blerchin/hangprinter/doc/v3/media/000.jpg

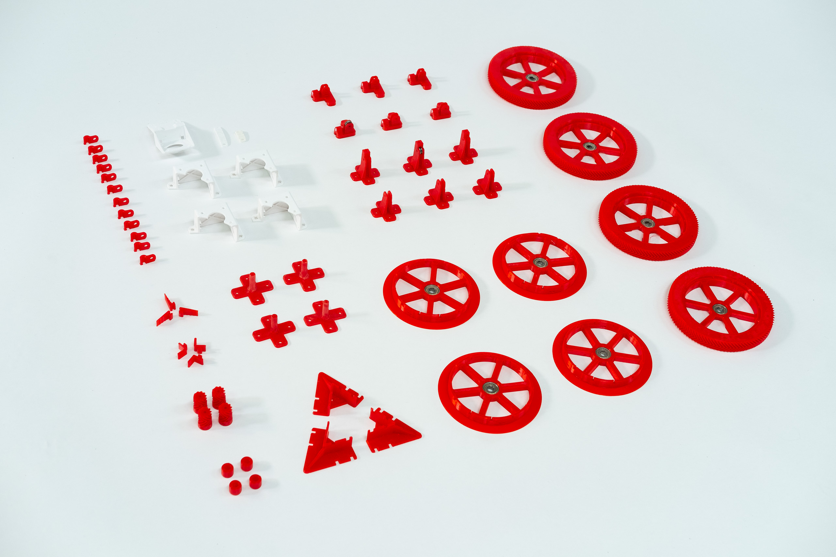
doc/v3/media/000.jpg
