blerchin/hangprinter/doc/v3/media/001.jpg

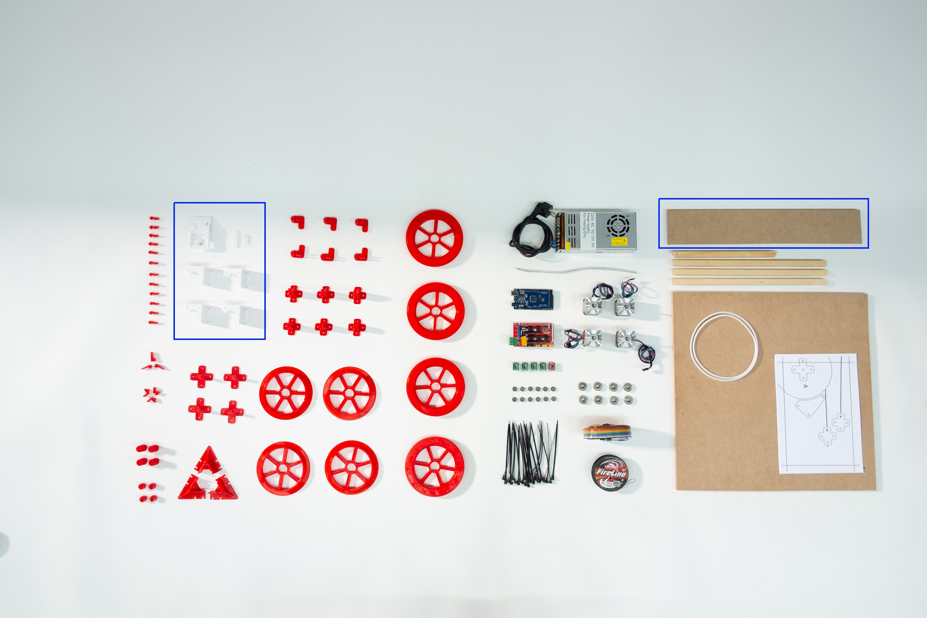
doc/v3/media/001.jpg
