blerchin/hangprinter/doc/v3/media/002.jpg

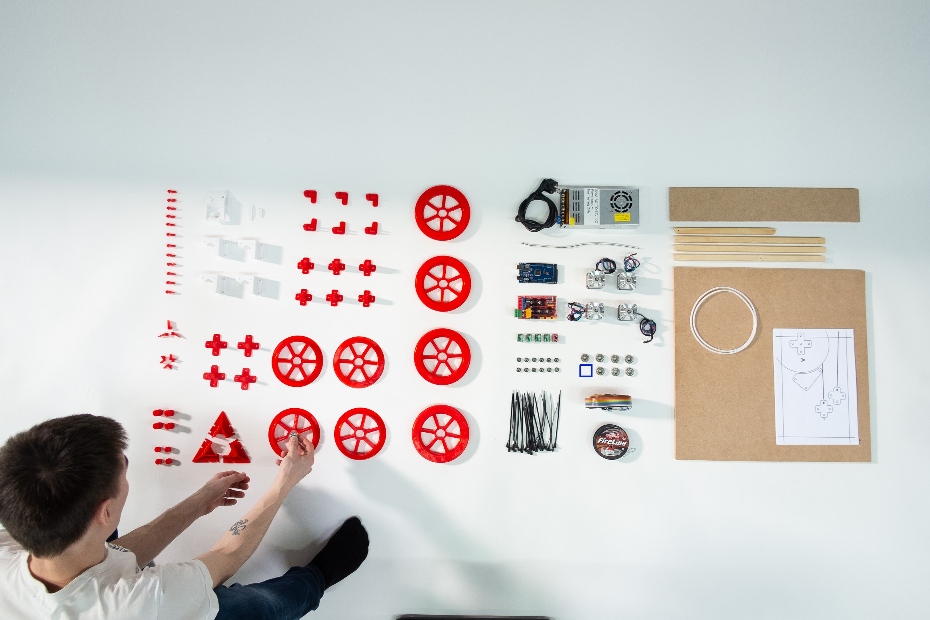
doc/v3/media/002.jpg
