blerchin/hangprinter/doc/v3/media/003.jpg

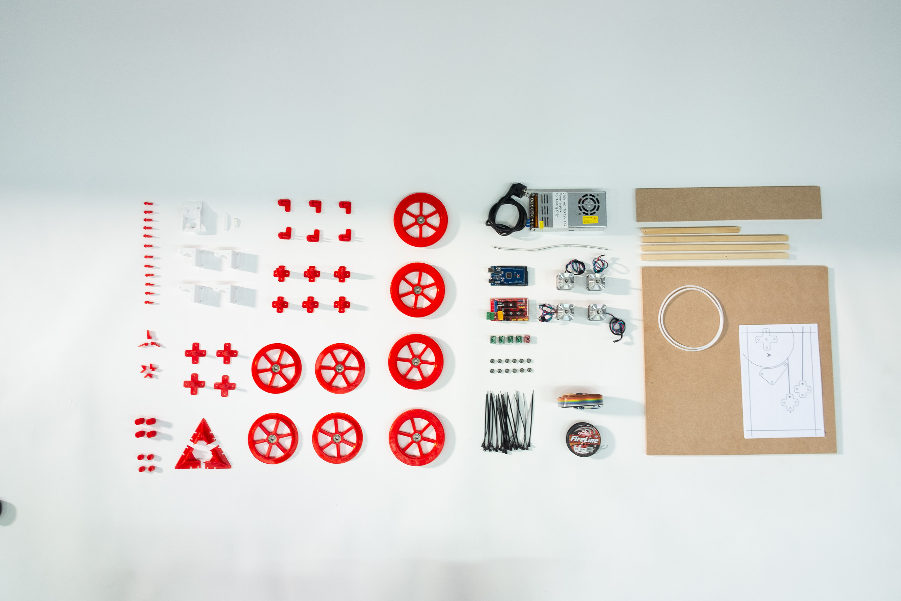
doc/v3/media/003.jpg
