blerchin/hangprinter/doc/v3/media/004.jpg

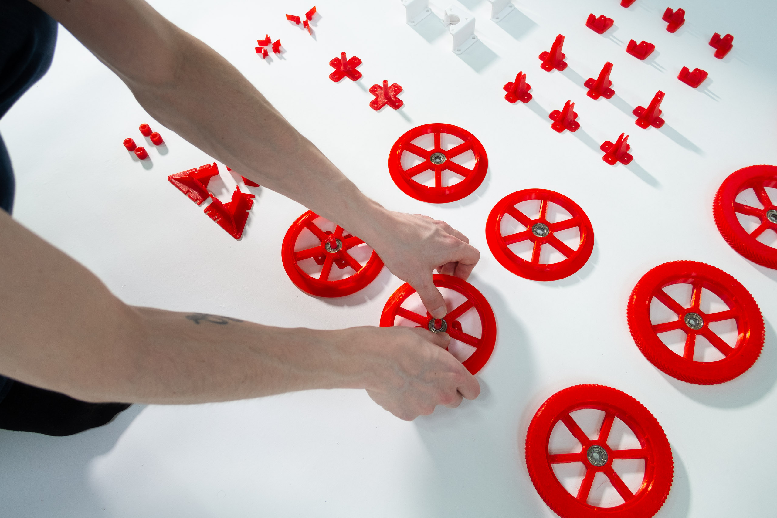
doc/v3/media/004.jpg
