blerchin/hangprinter/doc/v3/media/005.jpg

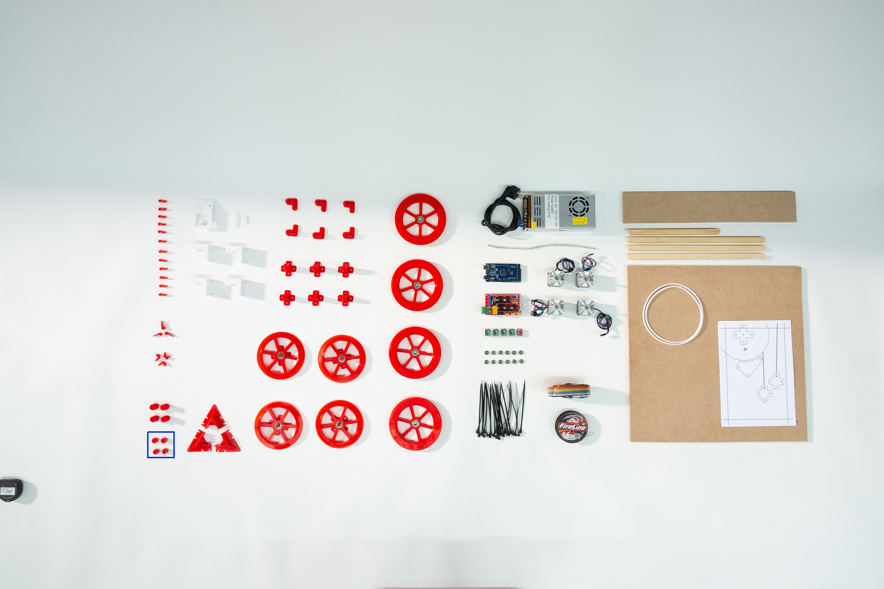
doc/v3/media/005.jpg
