blerchin/hangprinter/doc/v3/media/006.jpg

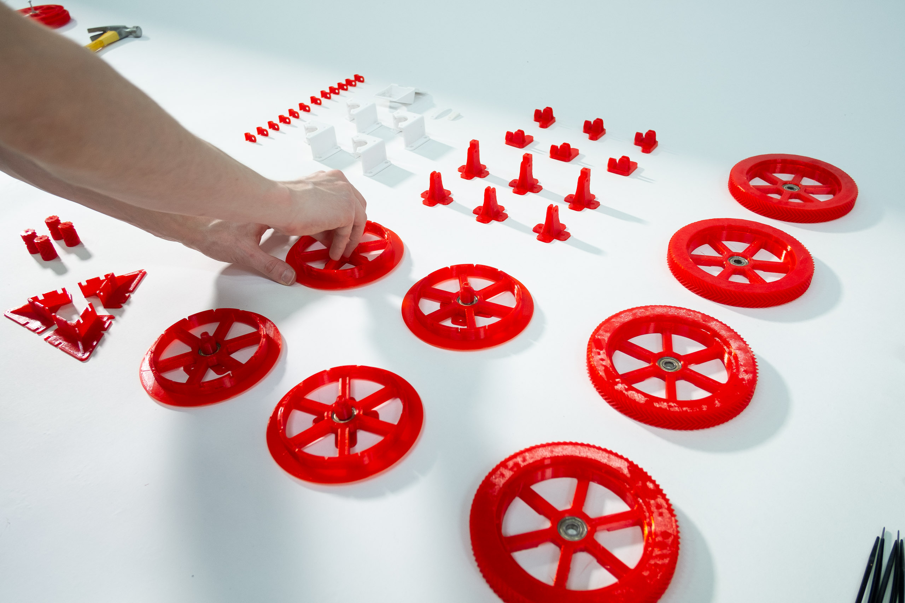
doc/v3/media/006.jpg
