blerchin/hangprinter/doc/v3/media/007.jpg

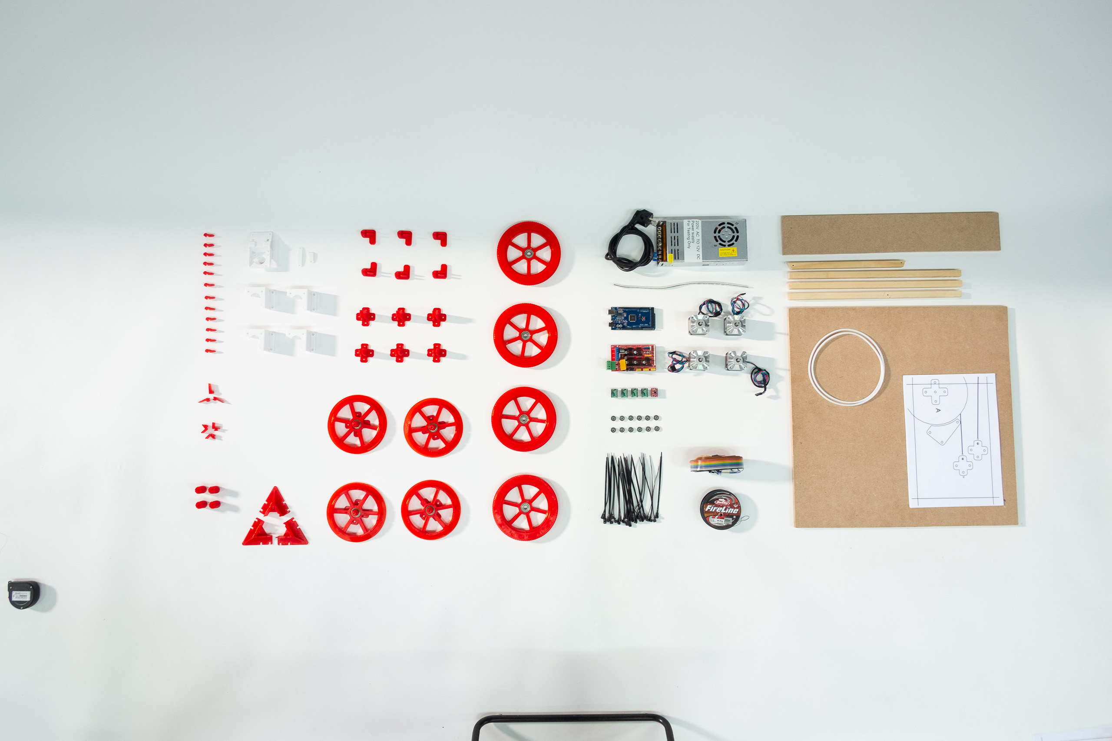
doc/v3/media/007.jpg
