blerchin/hangprinter/doc/v3/media/008.jpg

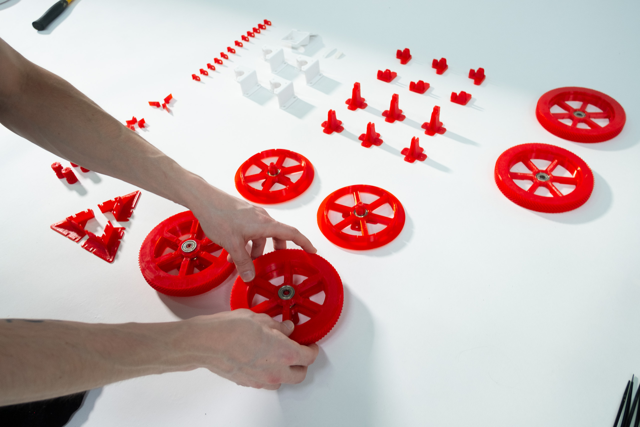
doc/v3/media/008.jpg
