blerchin/hangprinter/doc/v3/media/009.jpg

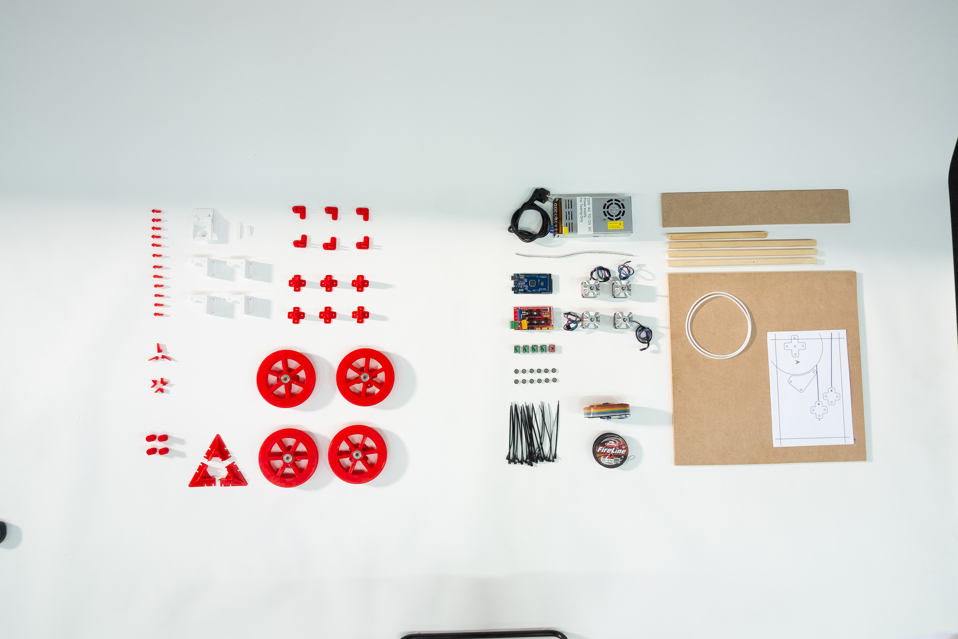
doc/v3/media/009.jpg
