blerchin/hangprinter/doc/v3/media/010.jpg

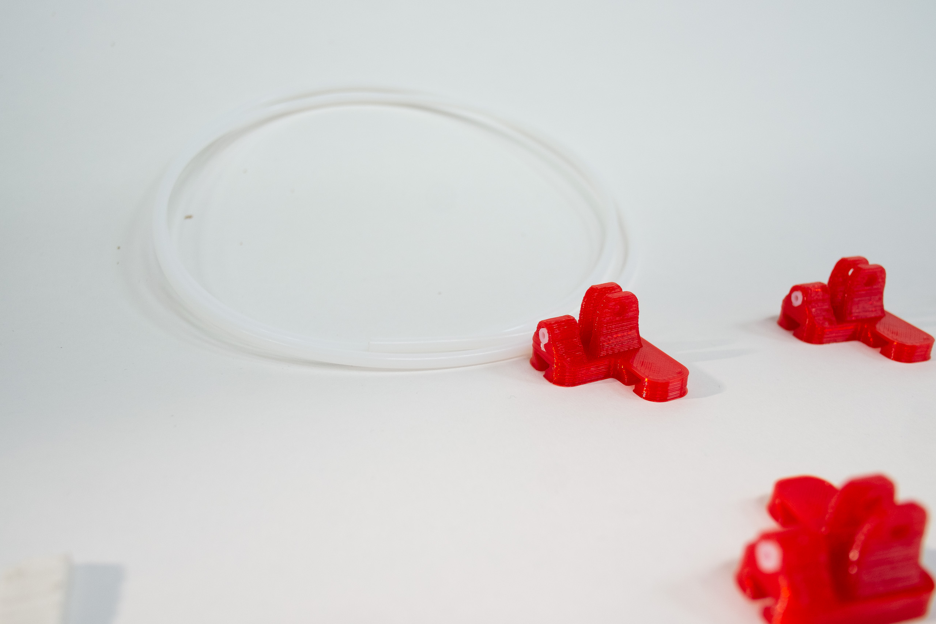
doc/v3/media/010.jpg
