blerchin/hangprinter/doc/v3/media/011.jpg

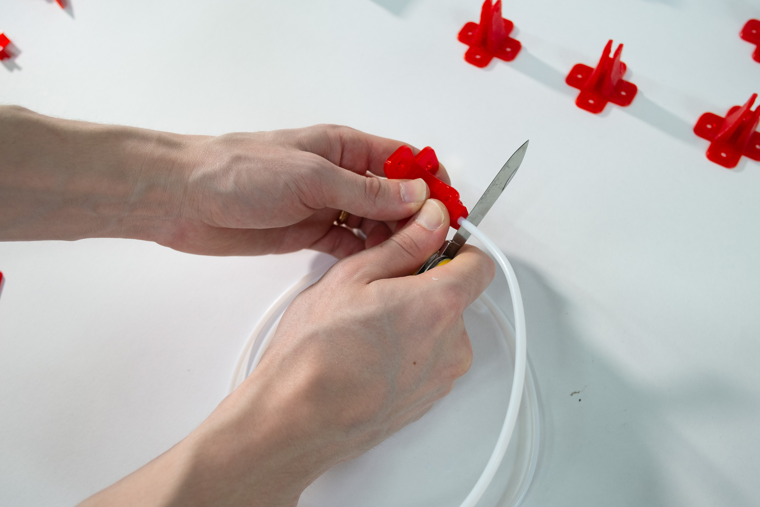
doc/v3/media/011.jpg
