blerchin/hangprinter/doc/v3/media/012.jpg

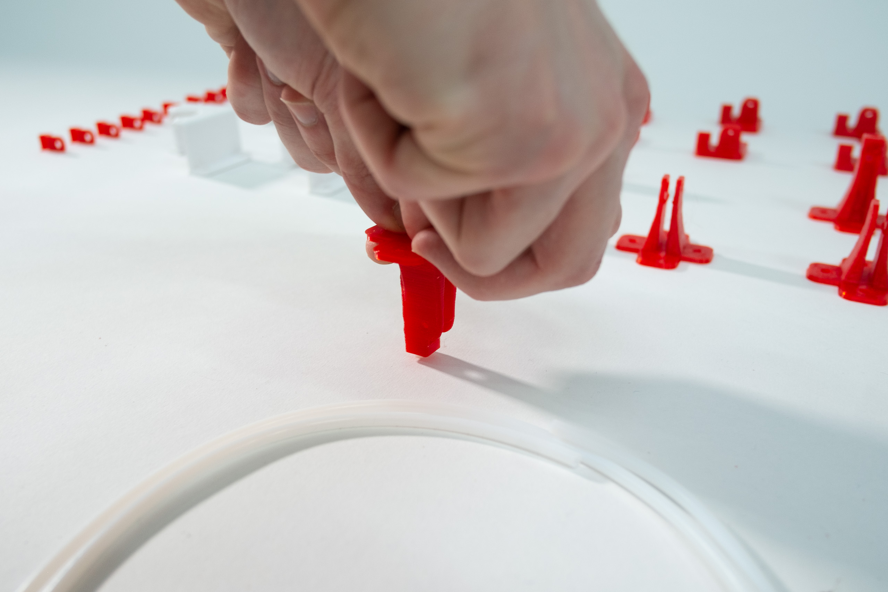
doc/v3/media/012.jpg
