blerchin/hangprinter/doc/v3/media/013.jpg

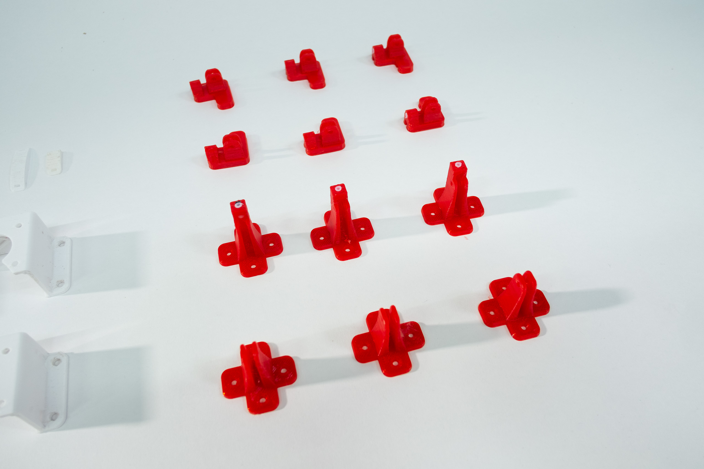
doc/v3/media/013.jpg
