blerchin/hangprinter/doc/v3/media/014.jpg

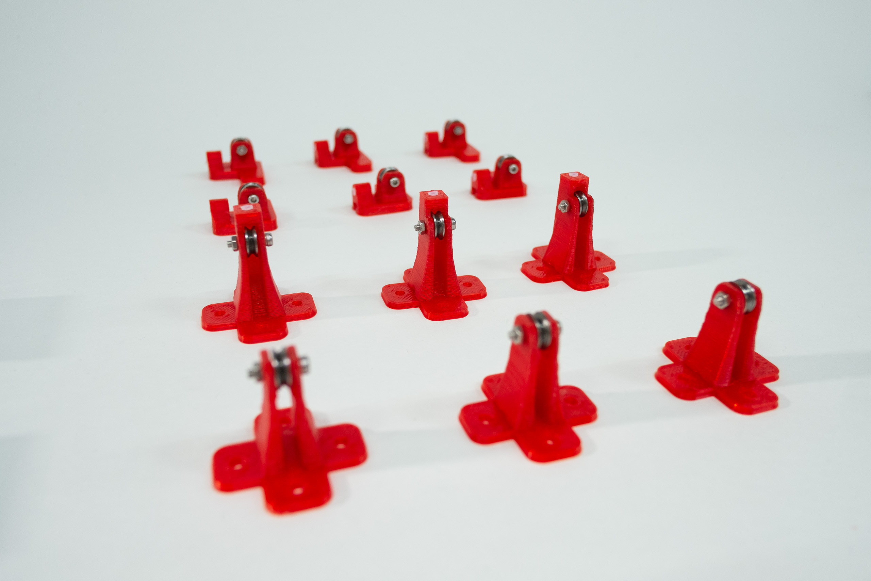
doc/v3/media/014.jpg
