blerchin/hangprinter/doc/v3/media/015.jpg

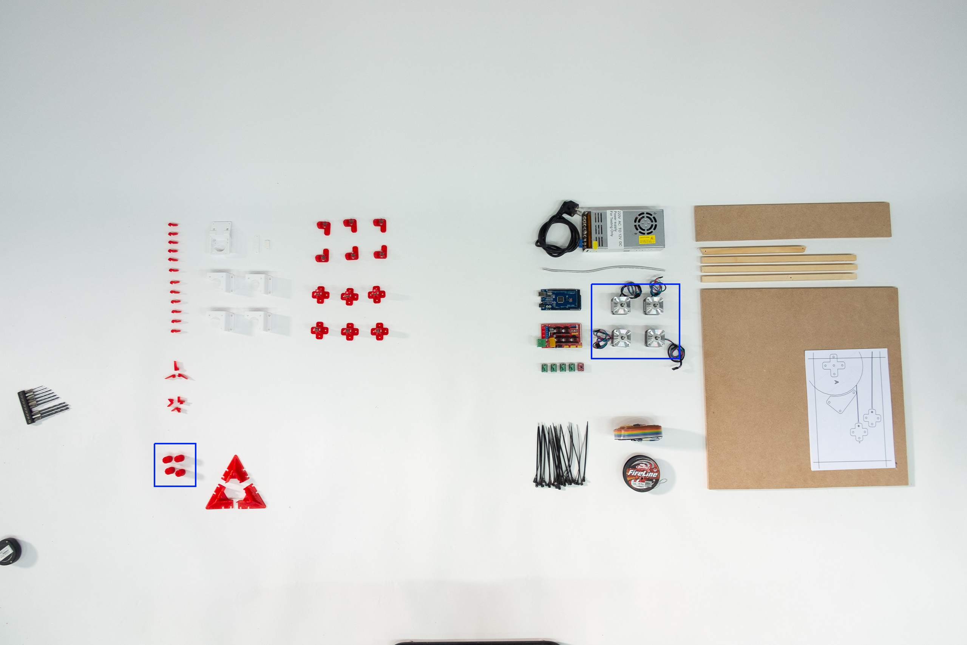
doc/v3/media/015.jpg
