blerchin/hangprinter/doc/v3/media/016.jpg

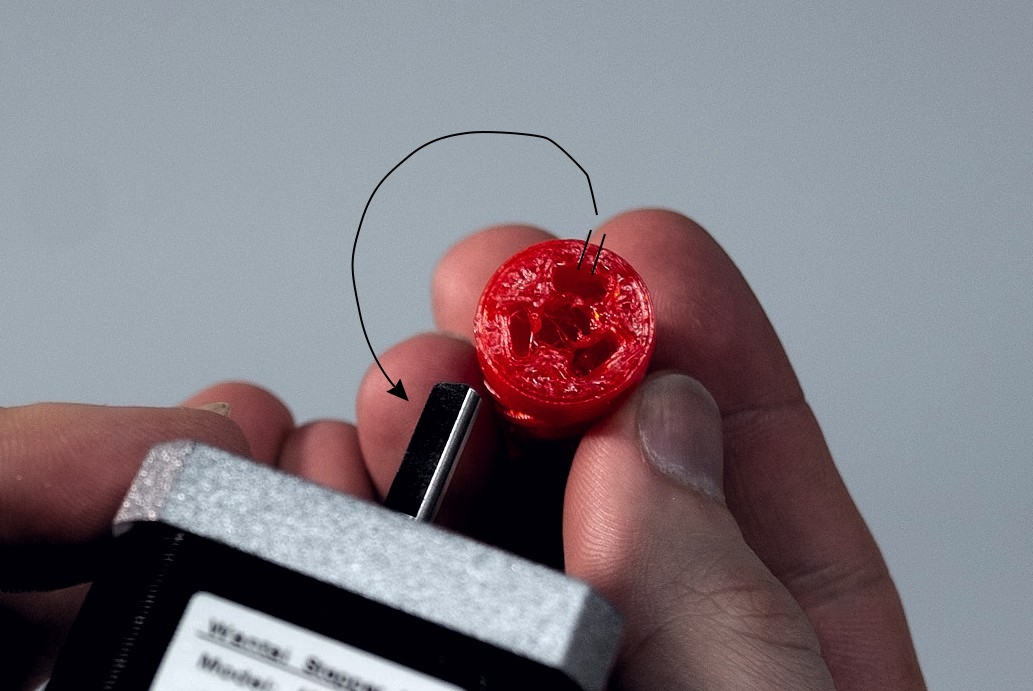
doc/v3/media/016.jpg
