blerchin/hangprinter/doc/v3/media/017.jpg

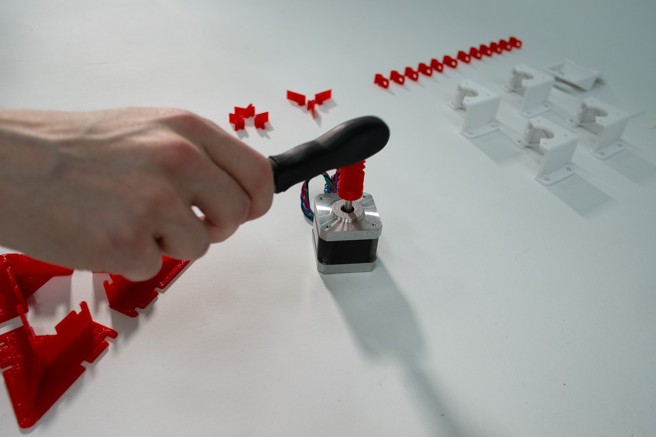
doc/v3/media/017.jpg
