blerchin/hangprinter/doc/v3/media/018.jpg

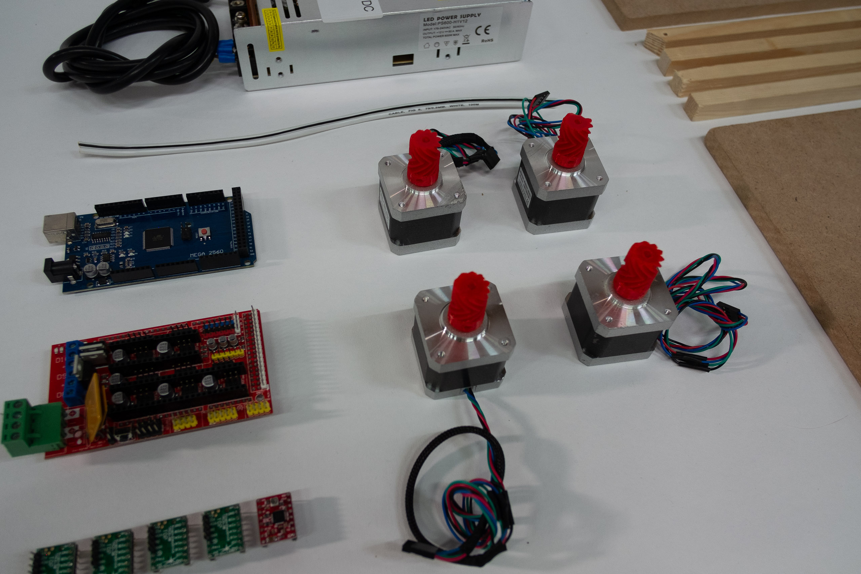
doc/v3/media/018.jpg
