blerchin/hangprinter/doc/v3/media/019.jpg

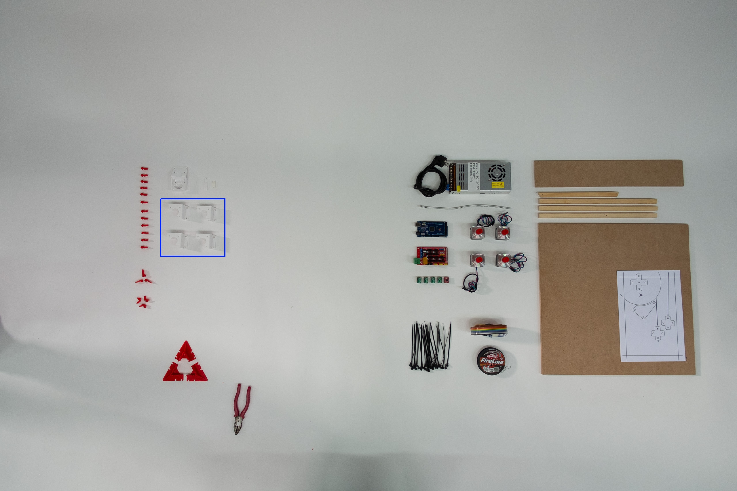
doc/v3/media/019.jpg
