blerchin/hangprinter/doc/v3/media/020.jpg

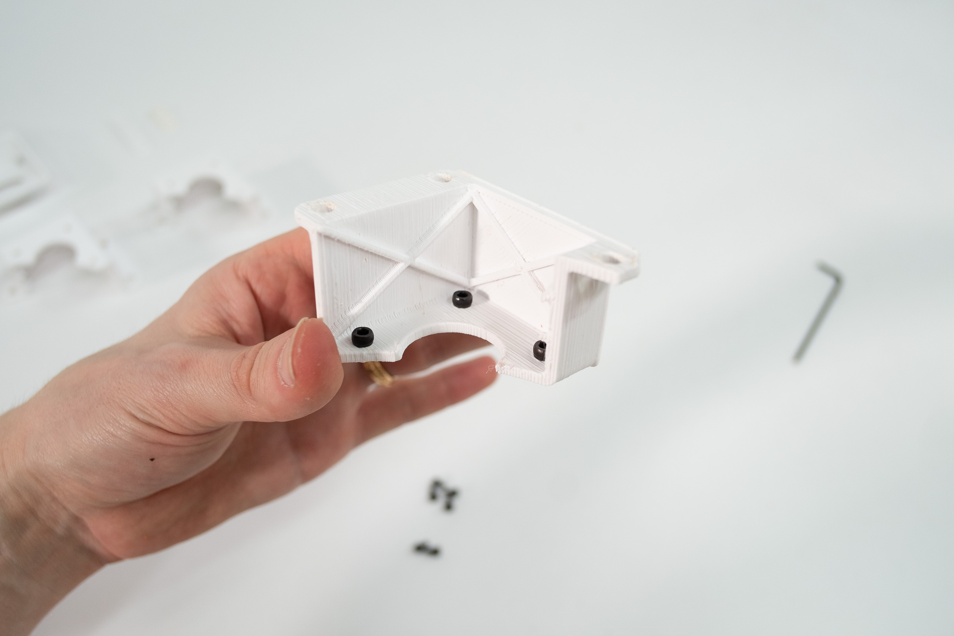
doc/v3/media/020.jpg
