blerchin/hangprinter/doc/v3/media/021.jpg

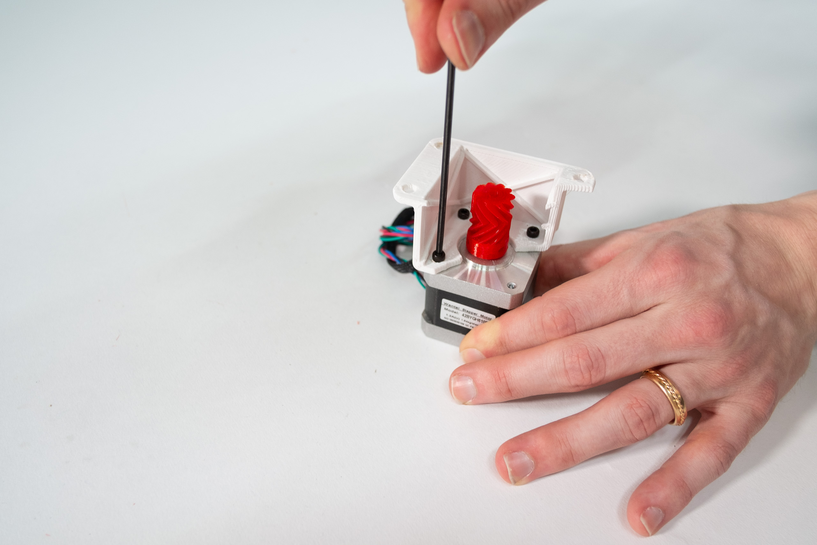
doc/v3/media/021.jpg
