blerchin/hangprinter/doc/v3/media/022.jpg

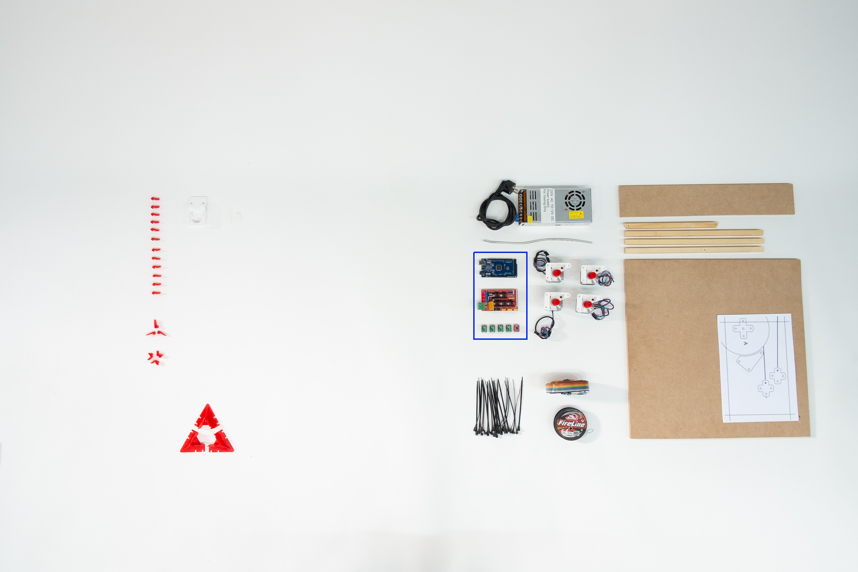
doc/v3/media/022.jpg
