blerchin/hangprinter/doc/v3/media/023.jpg

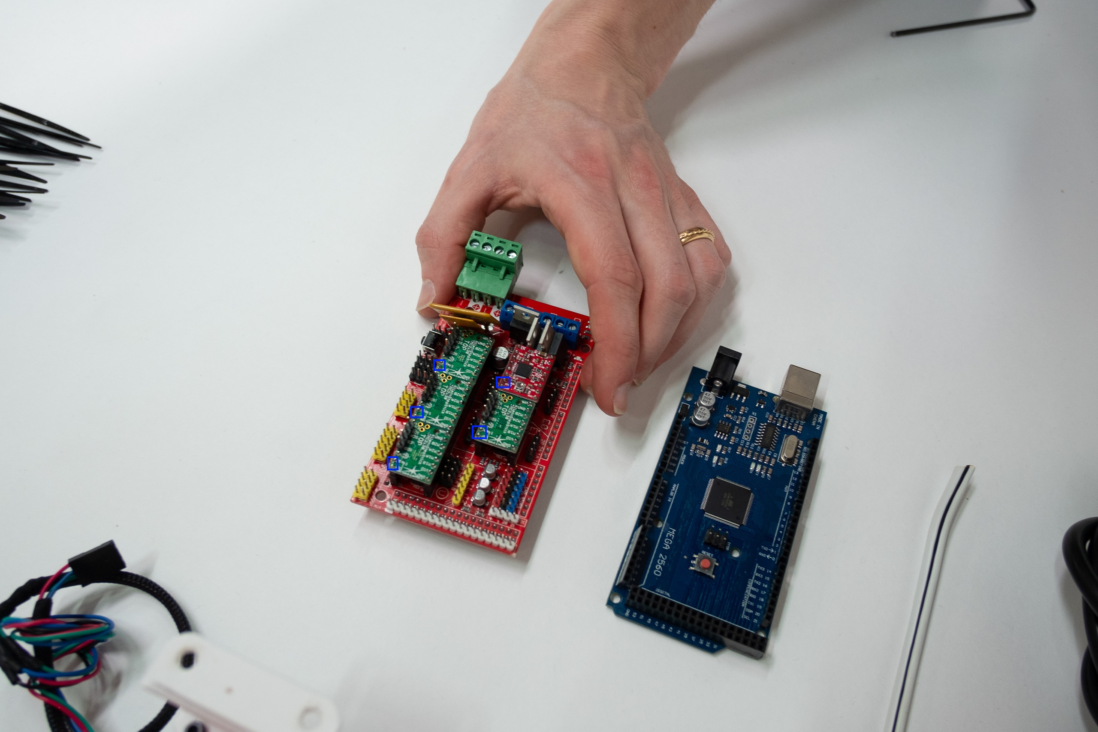
doc/v3/media/023.jpg
