blerchin/hangprinter/doc/v3/media/024.jpg

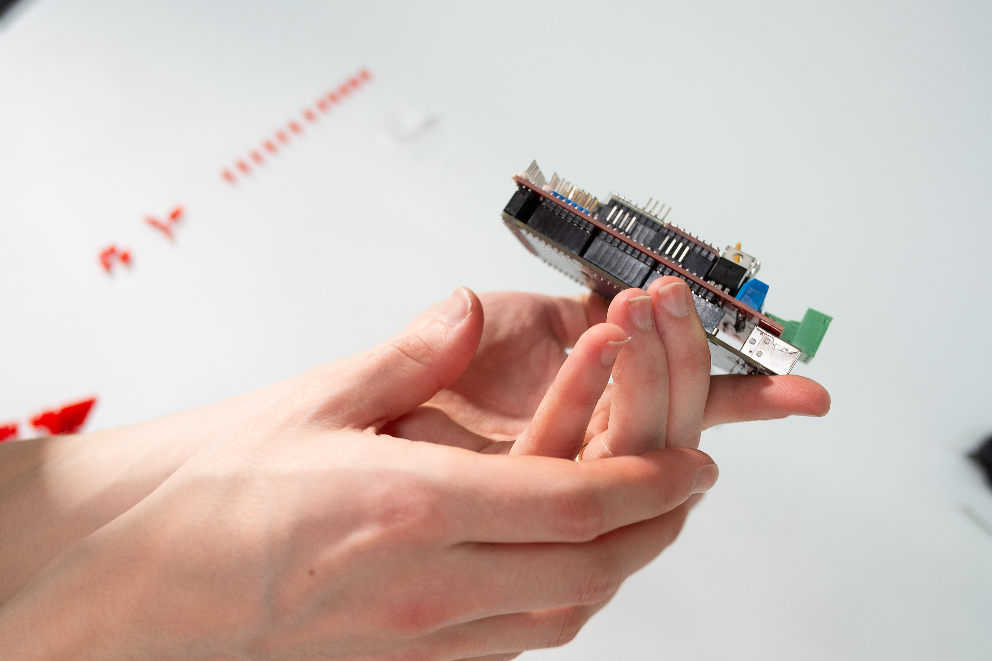
doc/v3/media/024.jpg
