blerchin/hangprinter/doc/v3/media/025.jpg

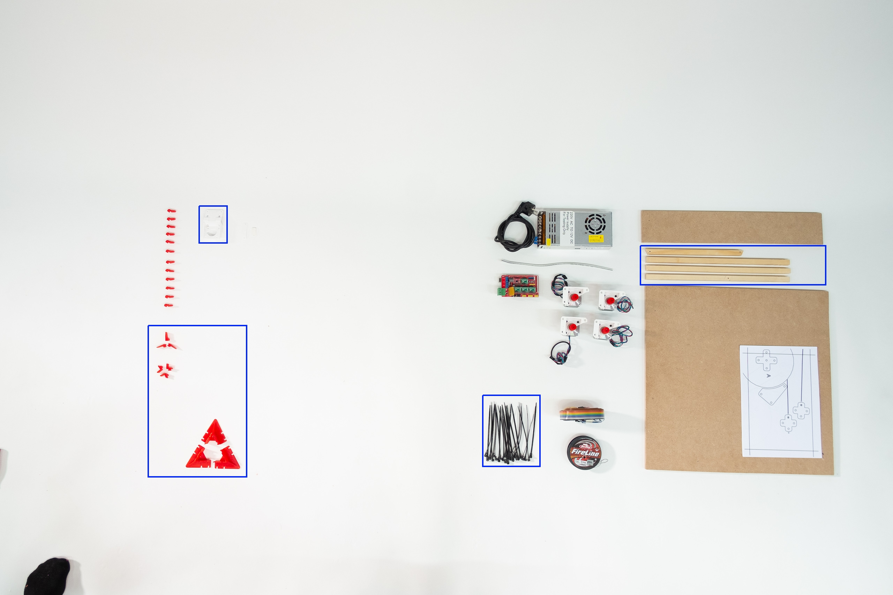
doc/v3/media/025.jpg
