blerchin/hangprinter/doc/v3/media/026.jpg

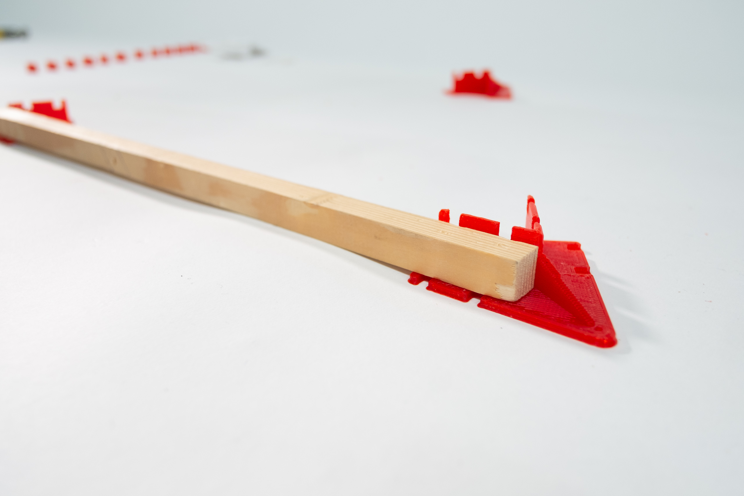
doc/v3/media/026.jpg
