blerchin/hangprinter/doc/v3/media/027.jpg

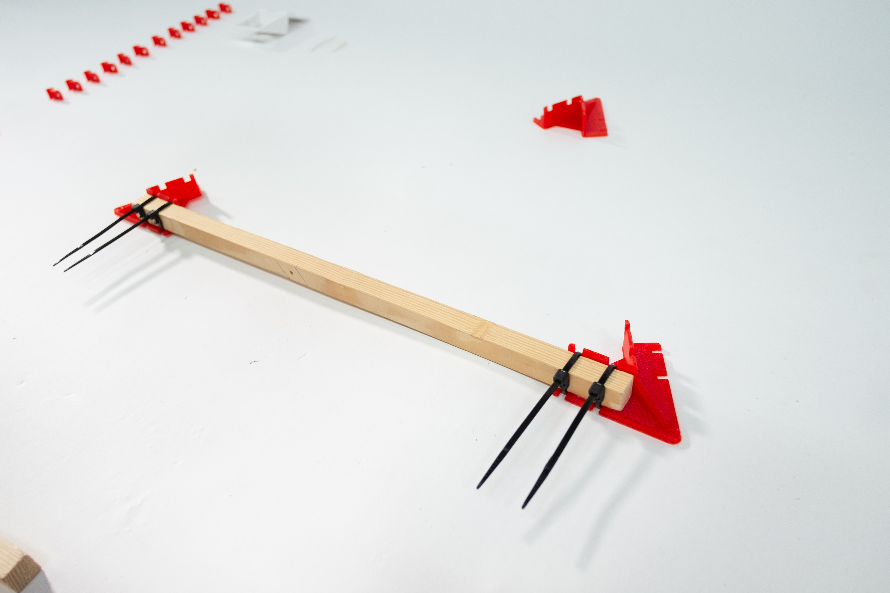
doc/v3/media/027.jpg
