blerchin/hangprinter/doc/v3/media/028.jpg

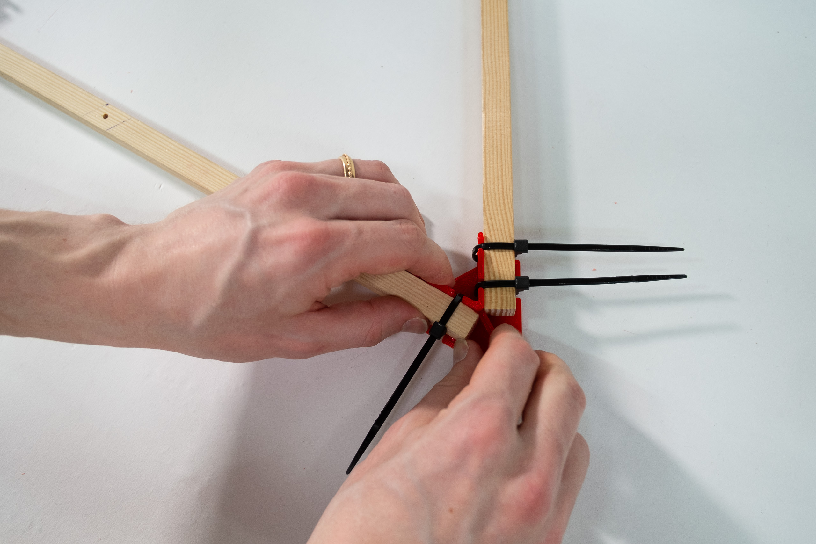
doc/v3/media/028.jpg
