blerchin/hangprinter/doc/v3/media/029.jpg

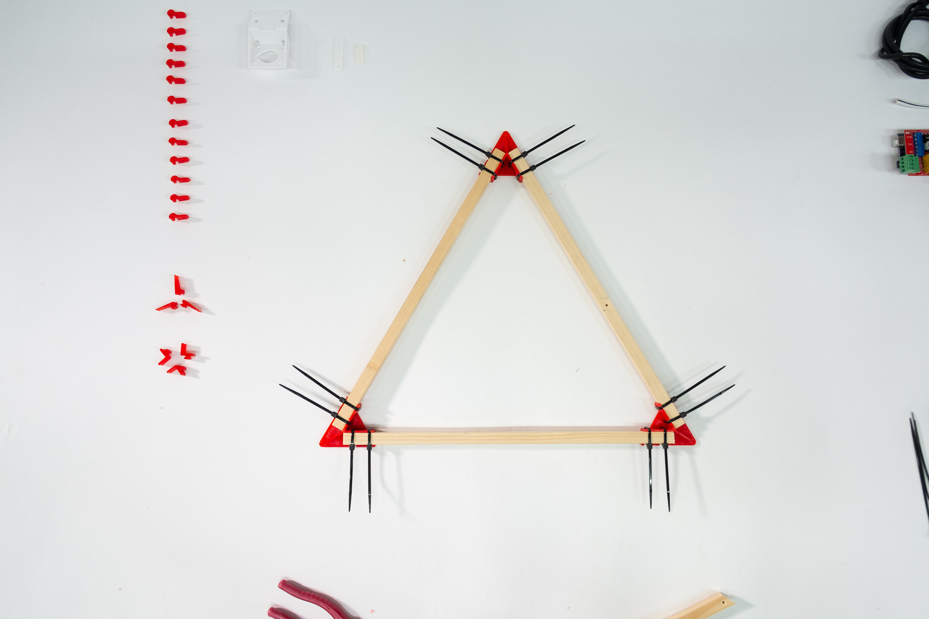
doc/v3/media/029.jpg
