blerchin/hangprinter/doc/v3/media/030.jpg

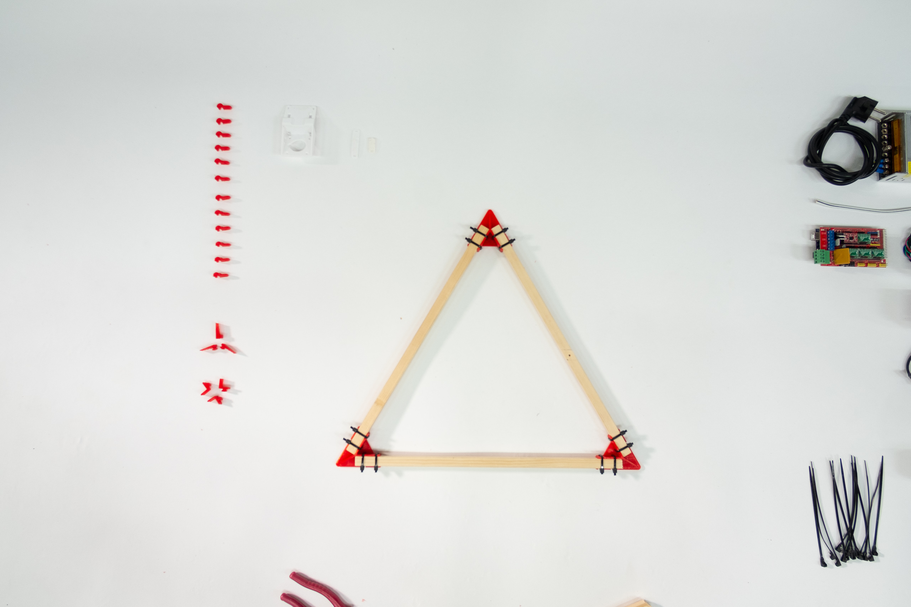
doc/v3/media/030.jpg
