blerchin/hangprinter/doc/v3/media/031.jpg

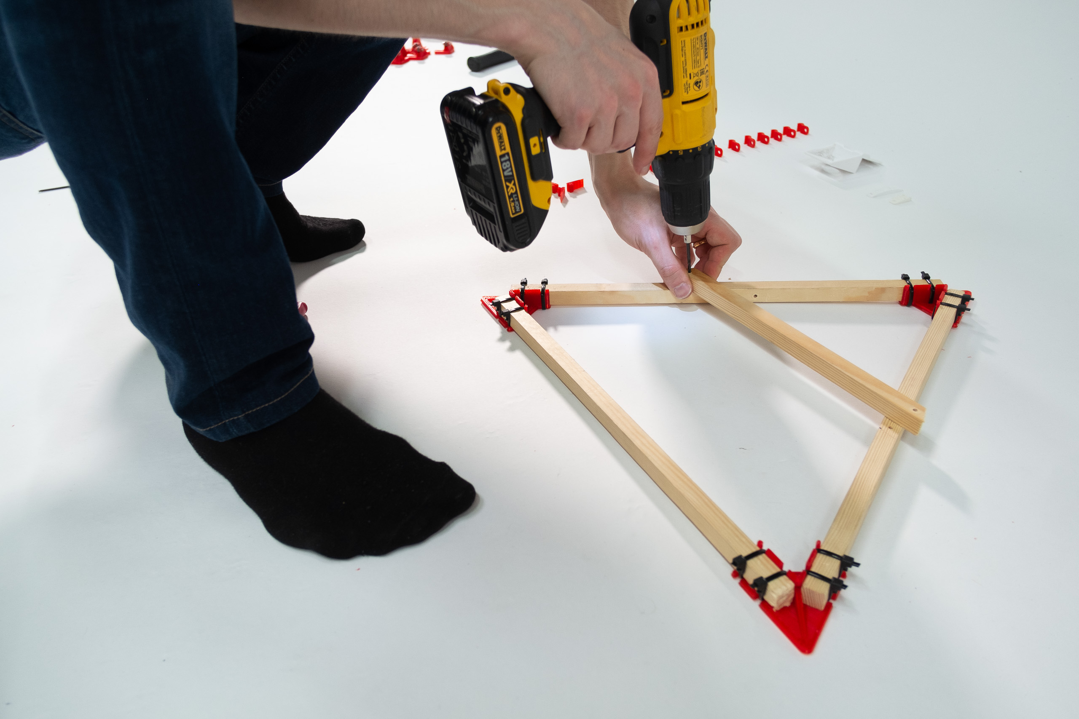
doc/v3/media/031.jpg
