blerchin/hangprinter/doc/v3/media/032.jpg

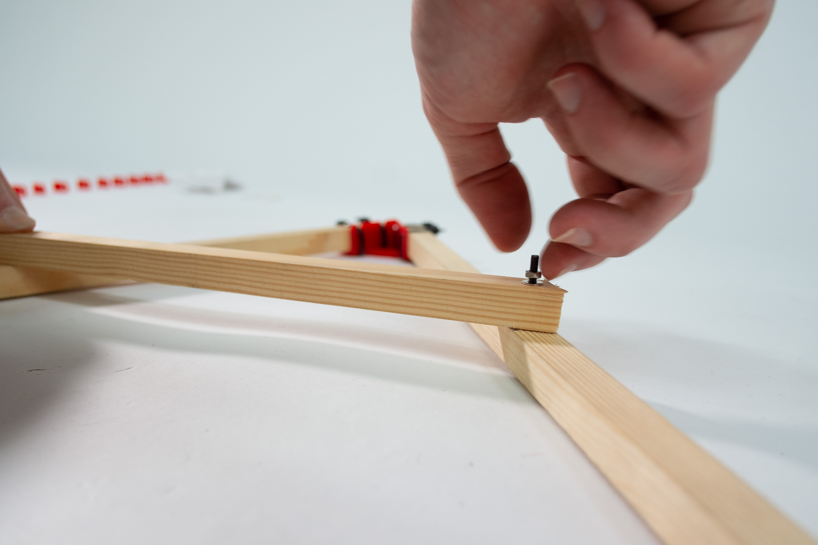
doc/v3/media/032.jpg
