blerchin/hangprinter/doc/v3/media/033.jpg

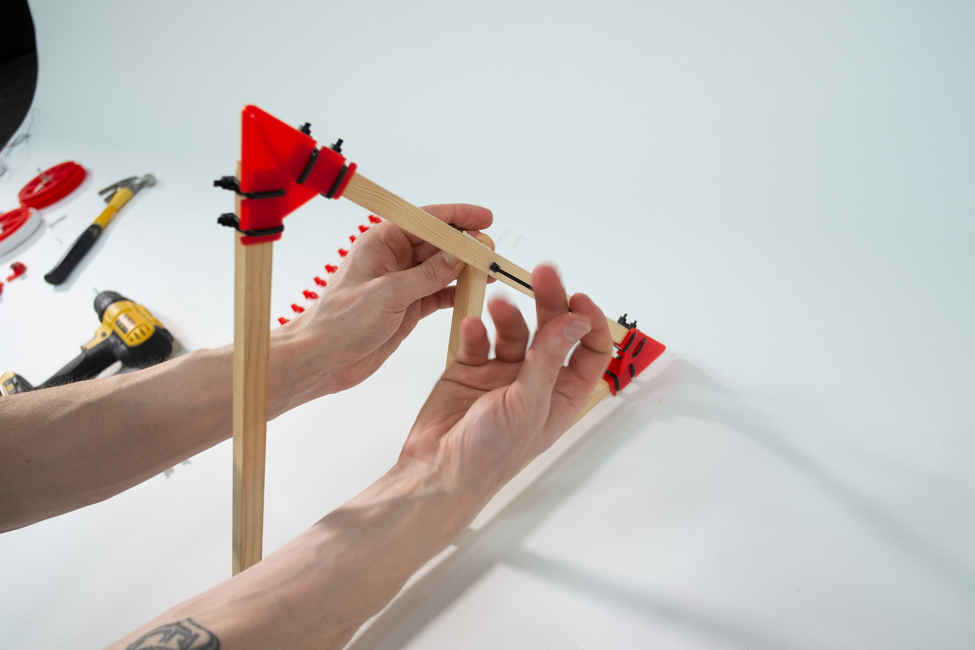
doc/v3/media/033.jpg
