blerchin/hangprinter/doc/v3/media/034.jpg

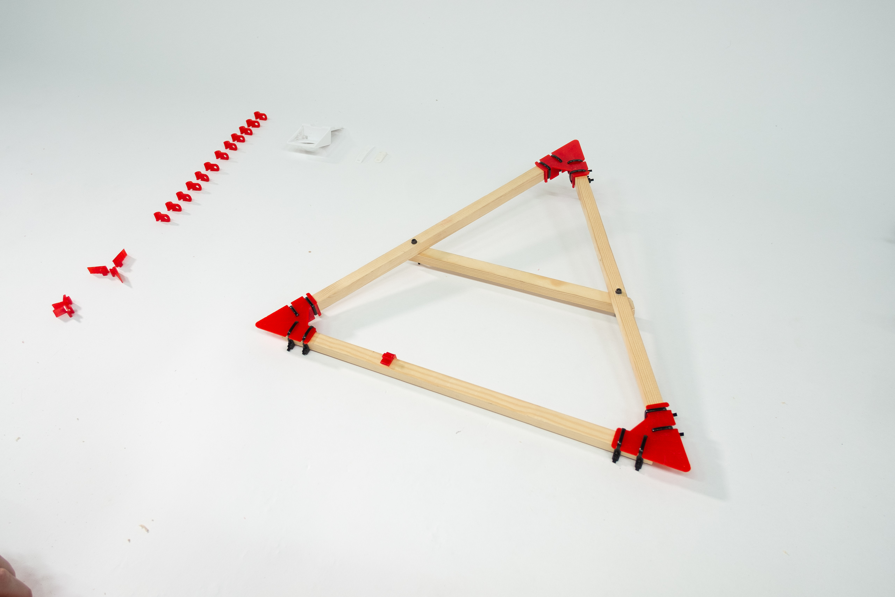
doc/v3/media/034.jpg
