blerchin/hangprinter/doc/v3/media/035.jpg

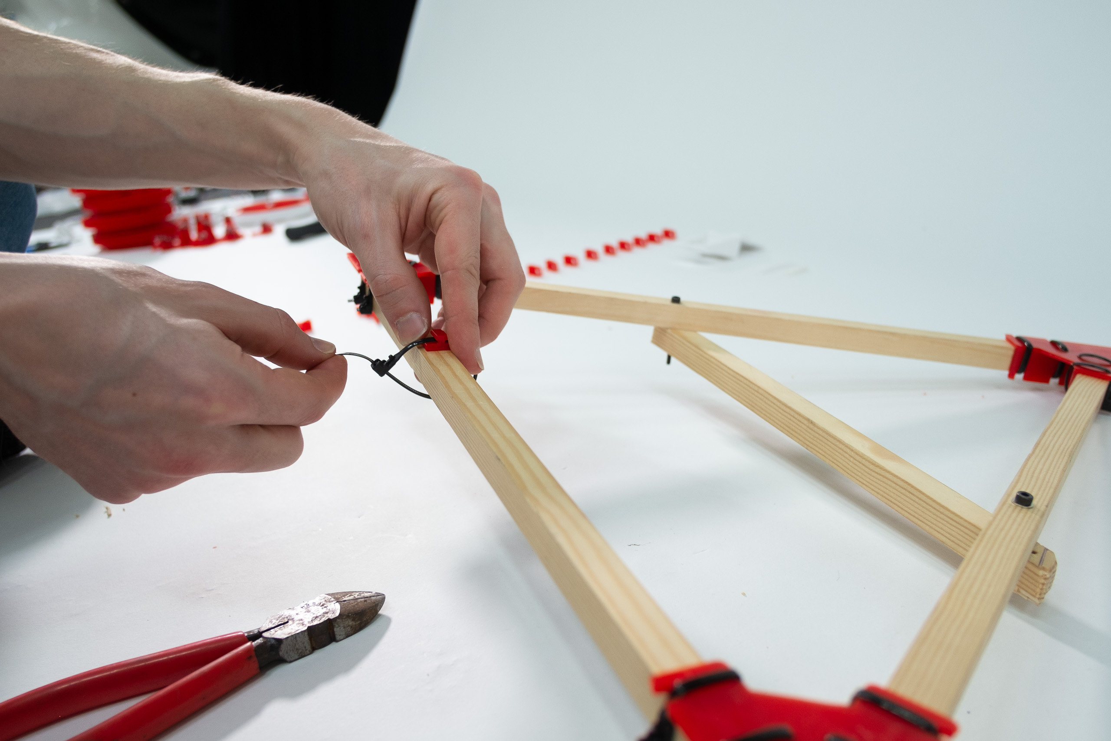
doc/v3/media/035.jpg
