blerchin/hangprinter/doc/v3/media/036.jpg

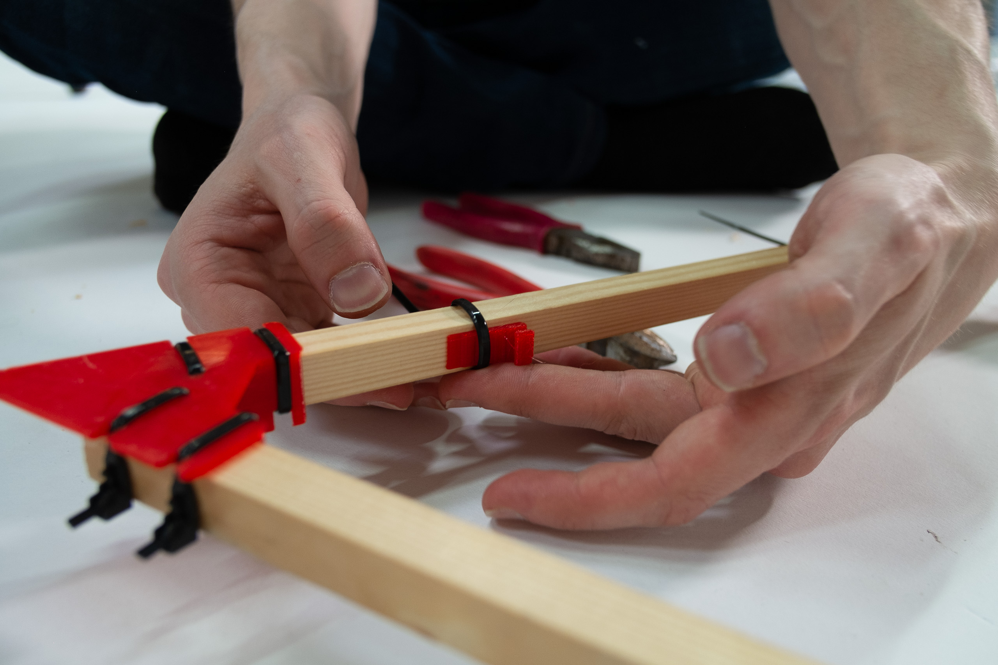
doc/v3/media/036.jpg
