blerchin/hangprinter/doc/v3/media/037.jpg

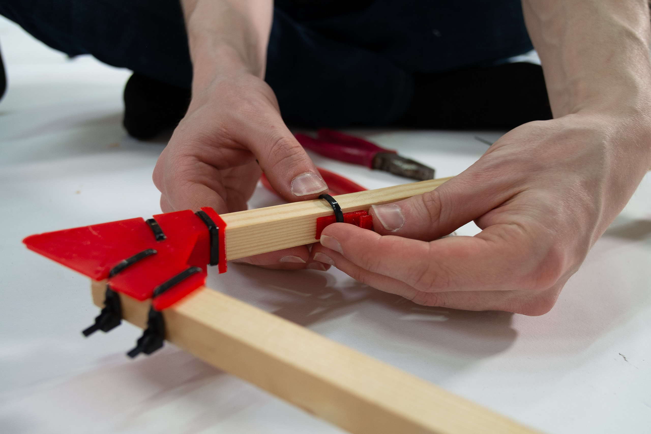
doc/v3/media/037.jpg
