blerchin/hangprinter/doc/v3/media/038.jpg

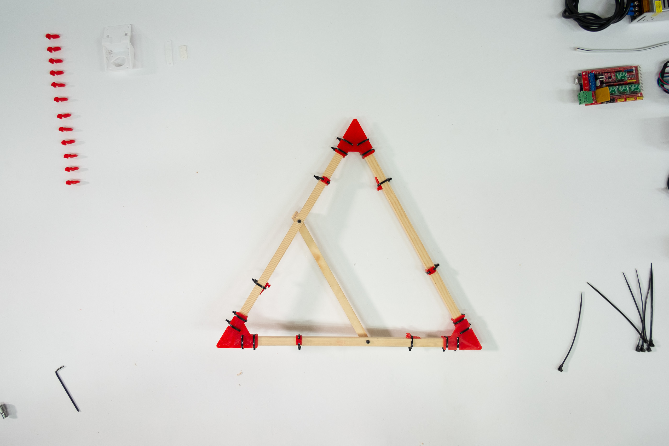
doc/v3/media/038.jpg
