blerchin/hangprinter/doc/v3/media/039.jpg

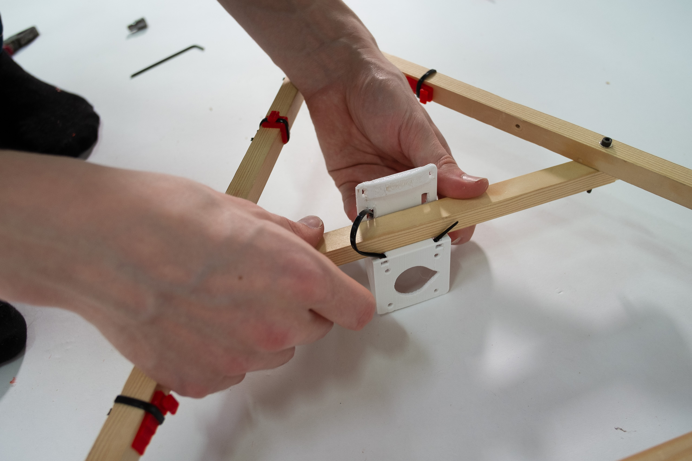
doc/v3/media/039.jpg
