blerchin/hangprinter/doc/v3/media/040.jpg

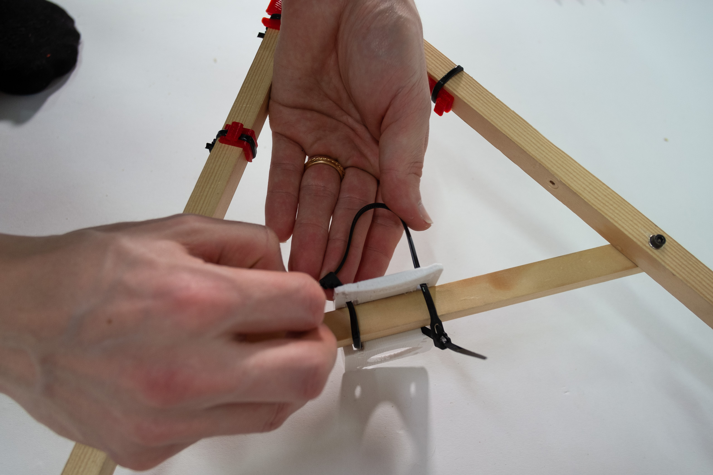
doc/v3/media/040.jpg
