blerchin/hangprinter/doc/v3/media/041.jpg

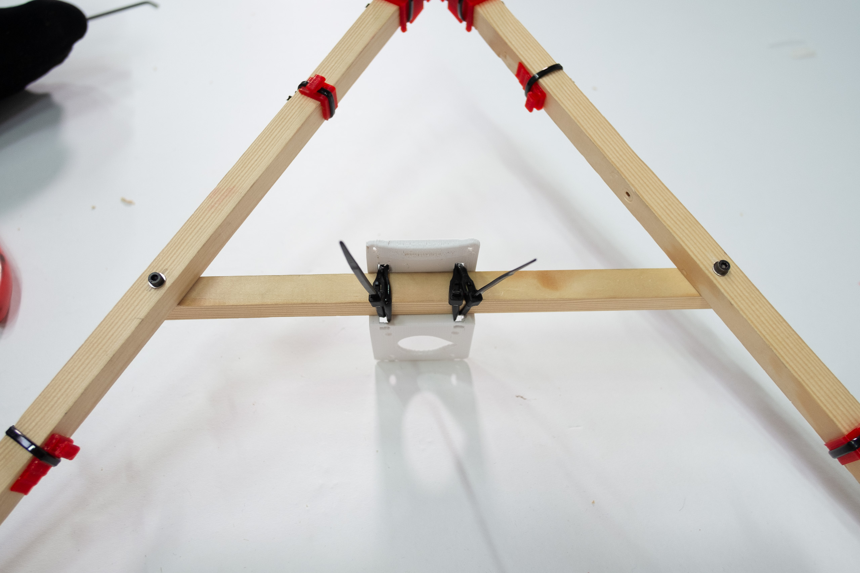
doc/v3/media/041.jpg
