blerchin/hangprinter/doc/v3/media/042.jpg

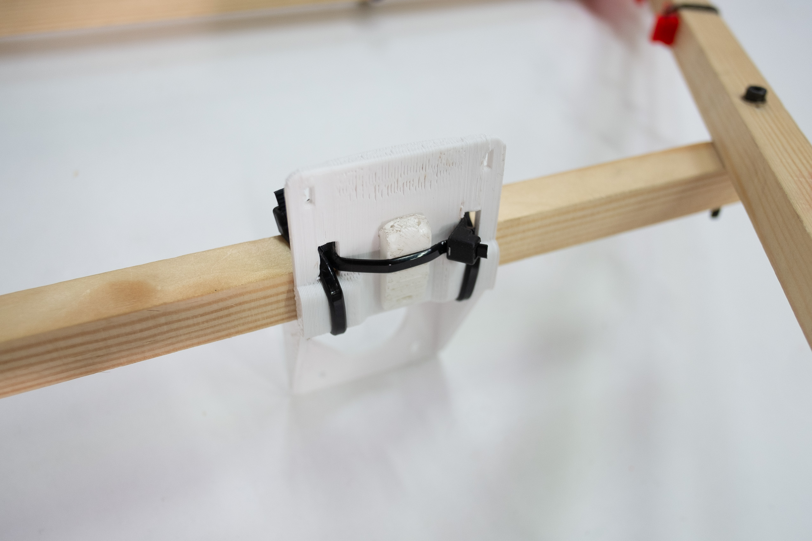
doc/v3/media/042.jpg
