blerchin/hangprinter/doc/v3/media/043.jpg

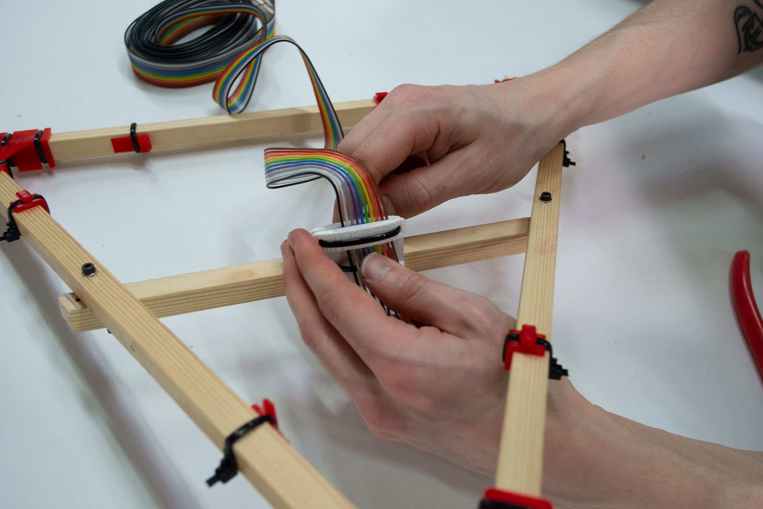
doc/v3/media/043.jpg
