blerchin/hangprinter/doc/v3/media/044.jpg

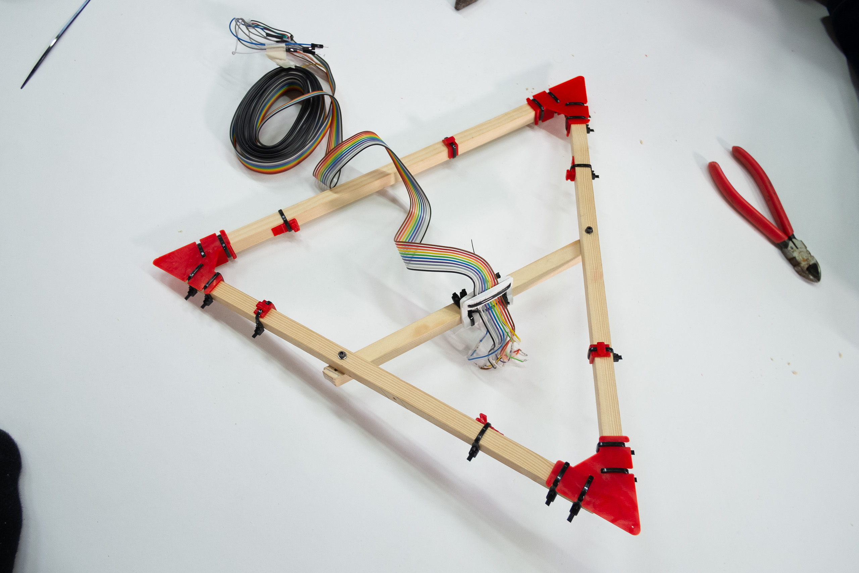
doc/v3/media/044.jpg
