blerchin/hangprinter/doc/v3/media/045.jpg

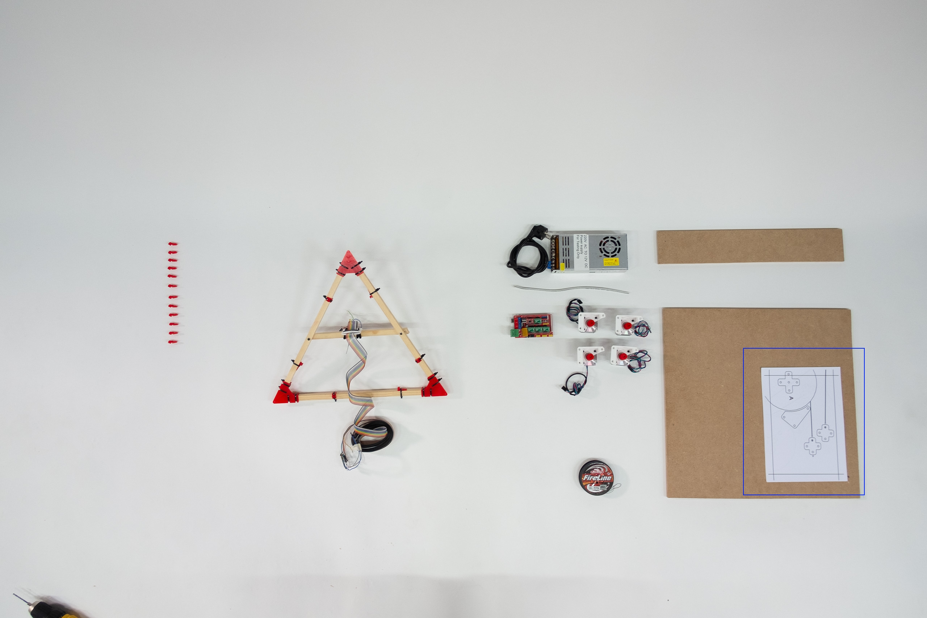
doc/v3/media/045.jpg
