blerchin/hangprinter/doc/v3/media/046.jpg

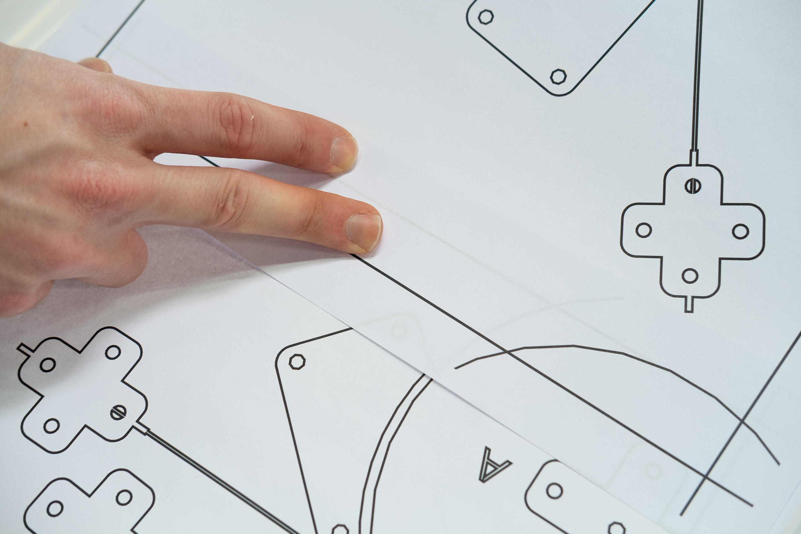
doc/v3/media/046.jpg
