blerchin/hangprinter/doc/v3/media/047.jpg

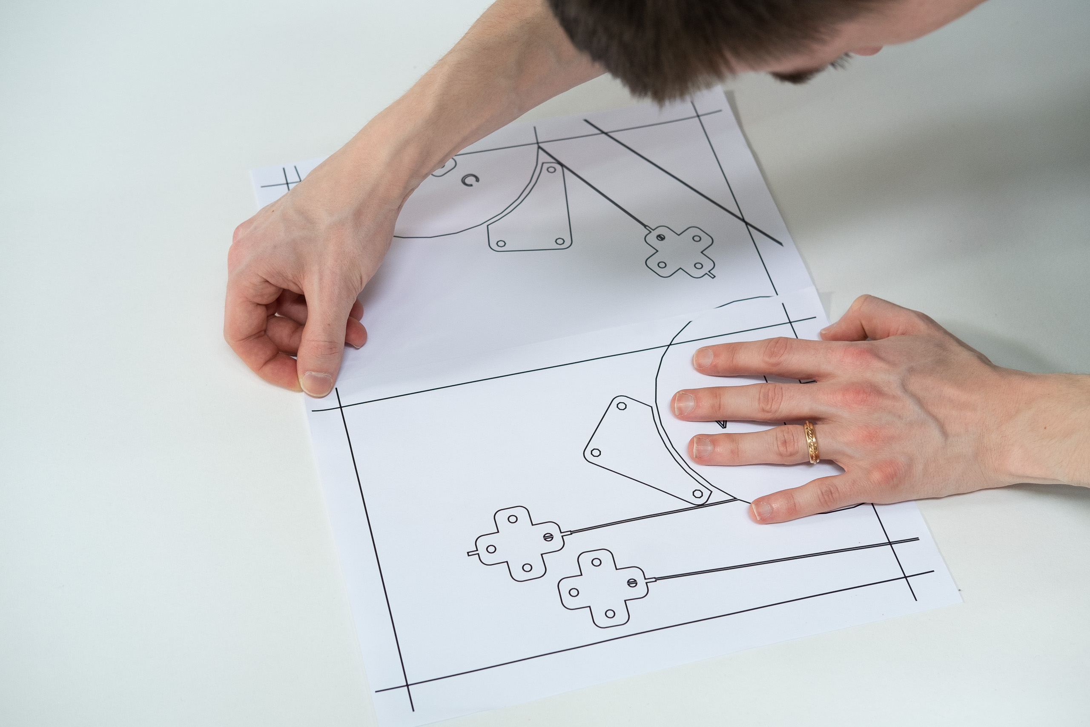
doc/v3/media/047.jpg
