blerchin/hangprinter/doc/v3/media/048.jpg

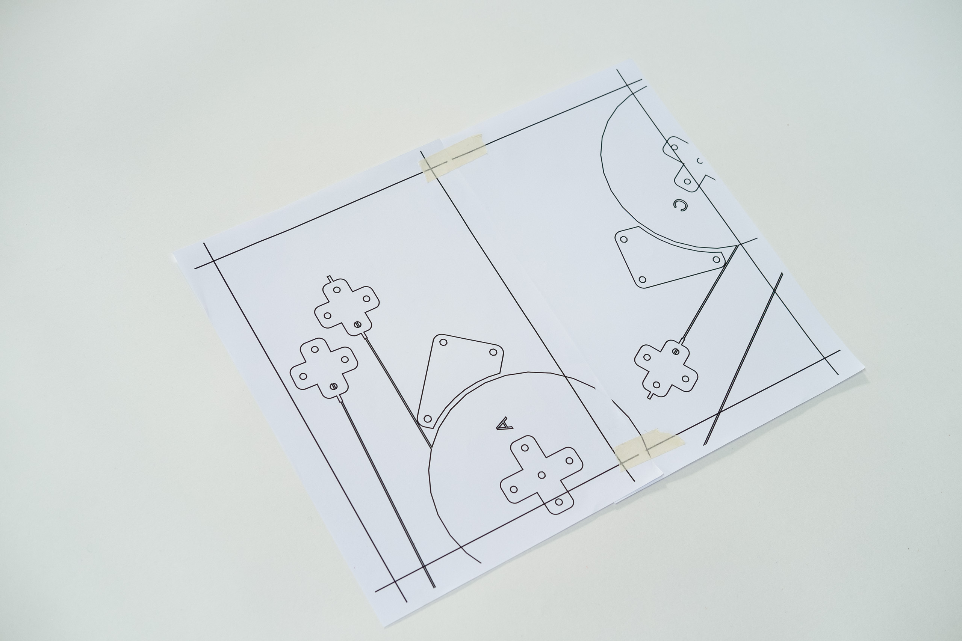
doc/v3/media/048.jpg
