blerchin/hangprinter/doc/v3/media/049.jpg

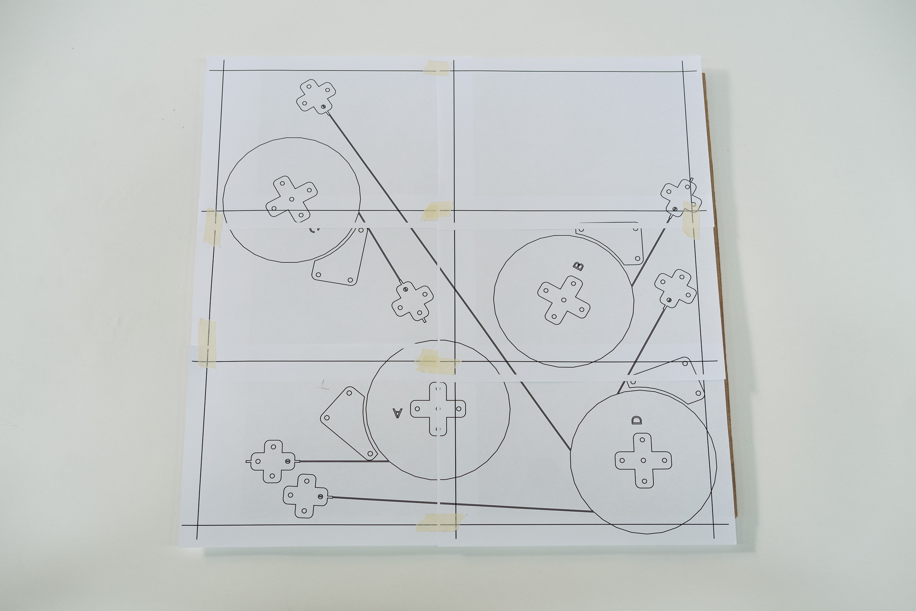
doc/v3/media/049.jpg
