blerchin/hangprinter/doc/v3/media/050.jpg

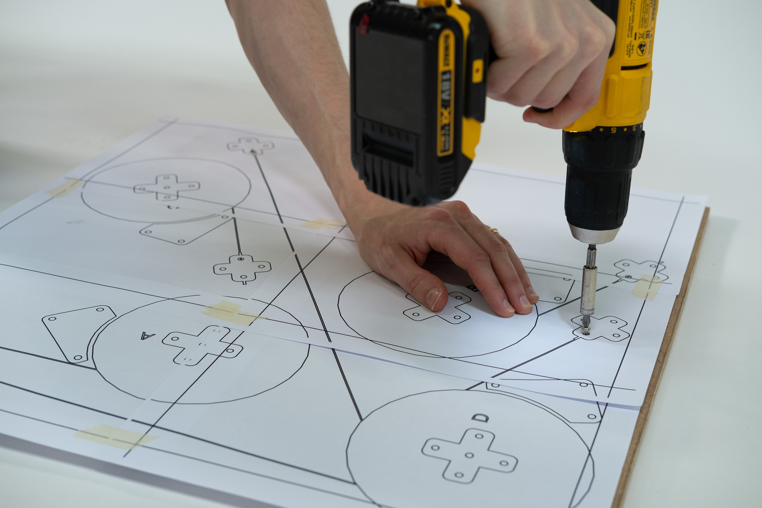
doc/v3/media/050.jpg
