blerchin/hangprinter/doc/v3/media/051.jpg

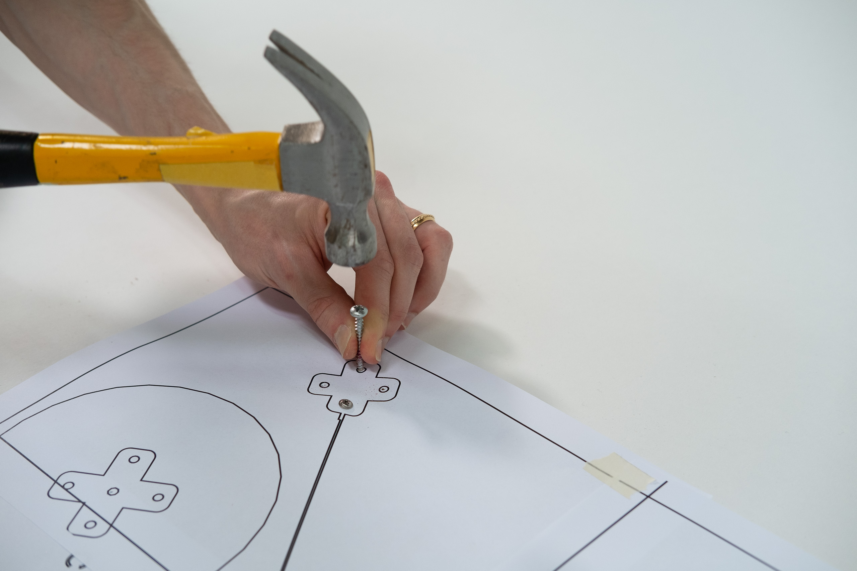
doc/v3/media/051.jpg
