blerchin/hangprinter/doc/v3/media/052.jpg

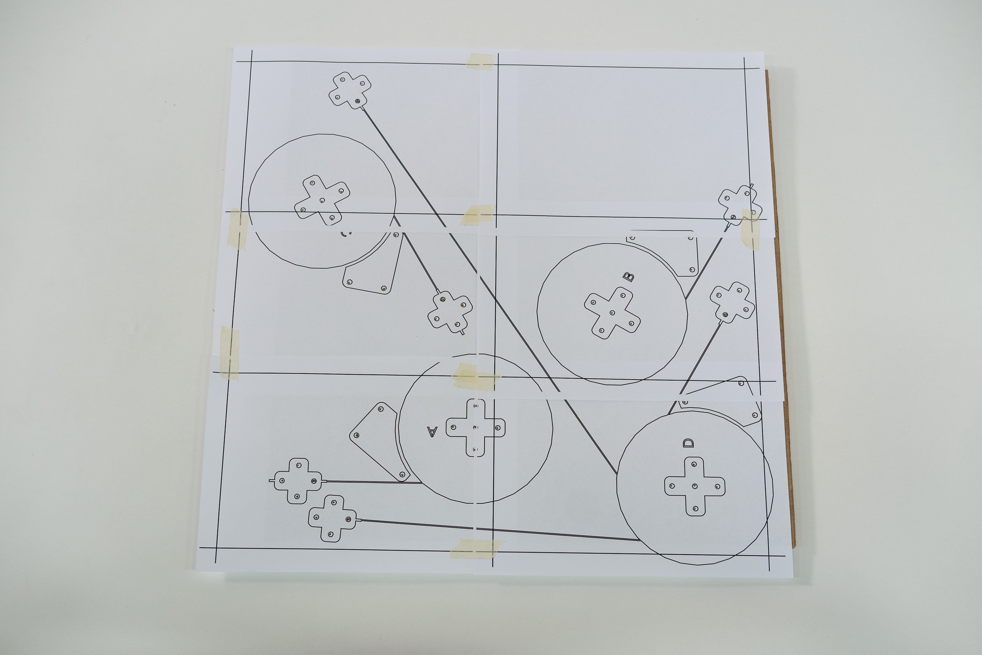
doc/v3/media/052.jpg
