blerchin/hangprinter/doc/v3/media/053.jpg

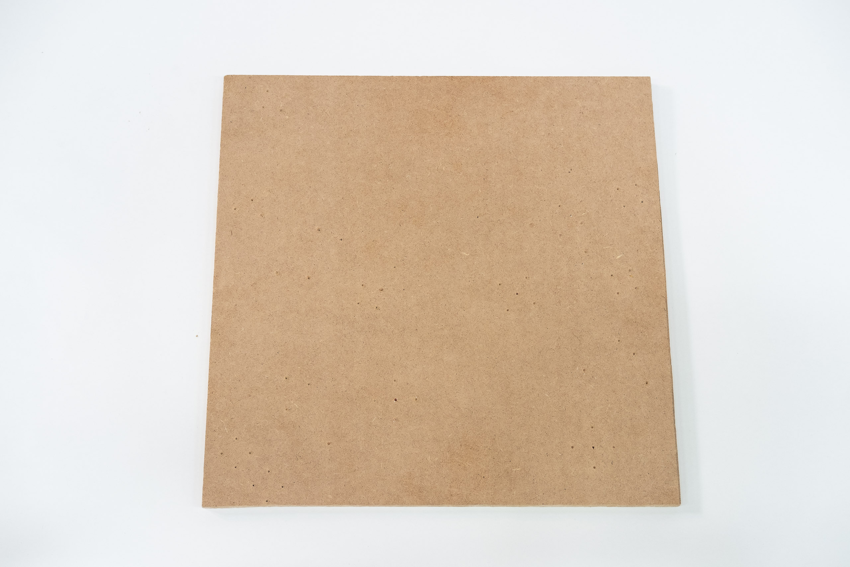
doc/v3/media/053.jpg
