blerchin/hangprinter/doc/v3/media/054.jpg

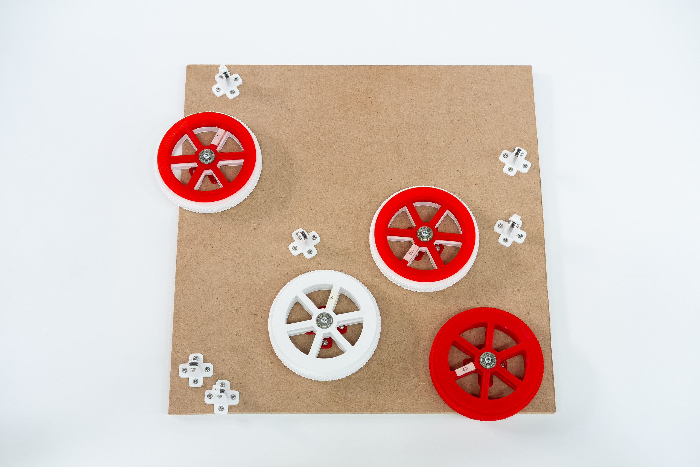
doc/v3/media/054.jpg
