blerchin/hangprinter/doc/v3/media/055.jpg

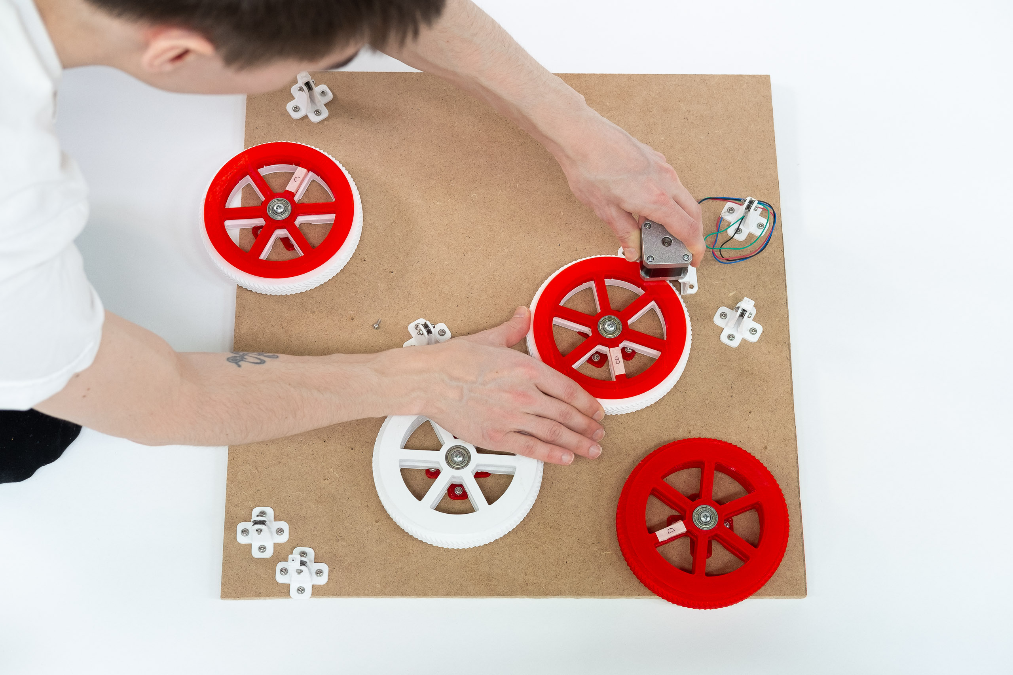
doc/v3/media/055.jpg
