blerchin/hangprinter/doc/v3/media/056.jpg

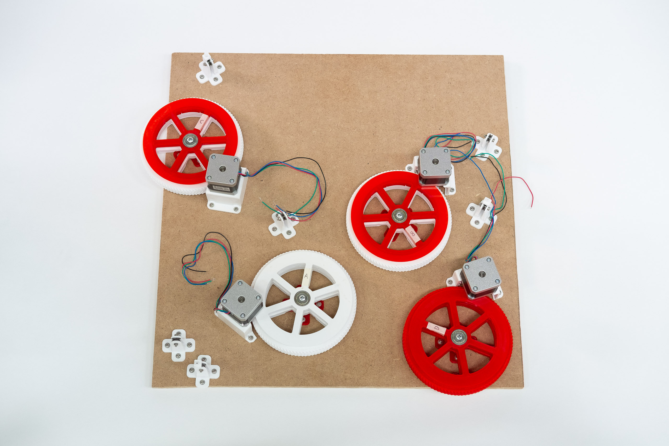
doc/v3/media/056.jpg
