blerchin/hangprinter/doc/v3/media/057.jpg

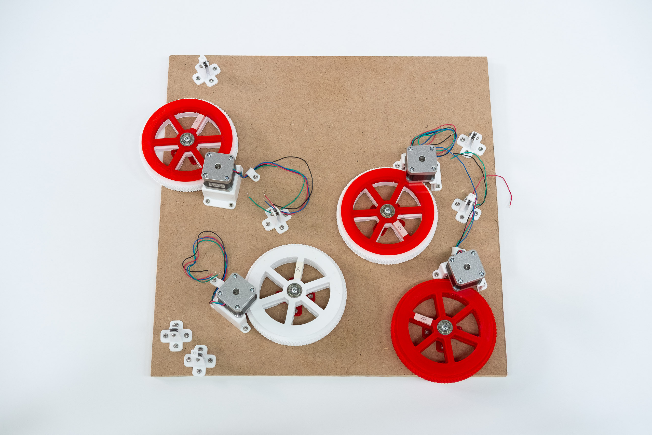
doc/v3/media/057.jpg
