blerchin/hangprinter/doc/v3/media/Hangprinter_Hitch_0.JPG

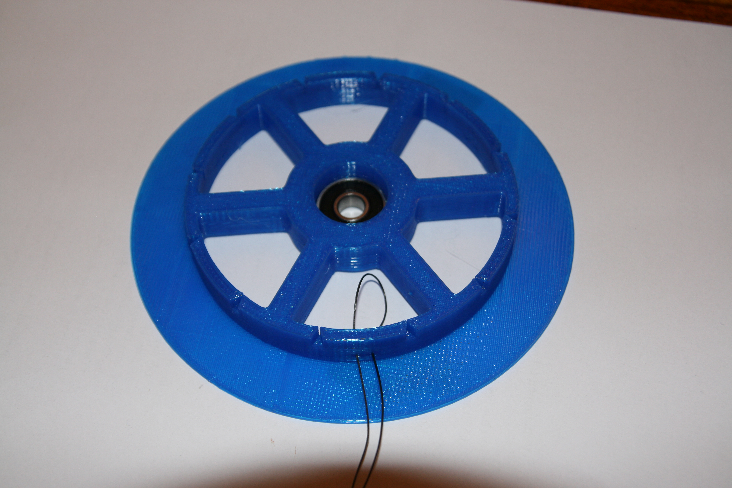
doc/v3/media/Hangprinter_Hitch_0.JPG
