blerchin/hangprinter/doc/v3/media/Hangprinter_Hitch_1.JPG

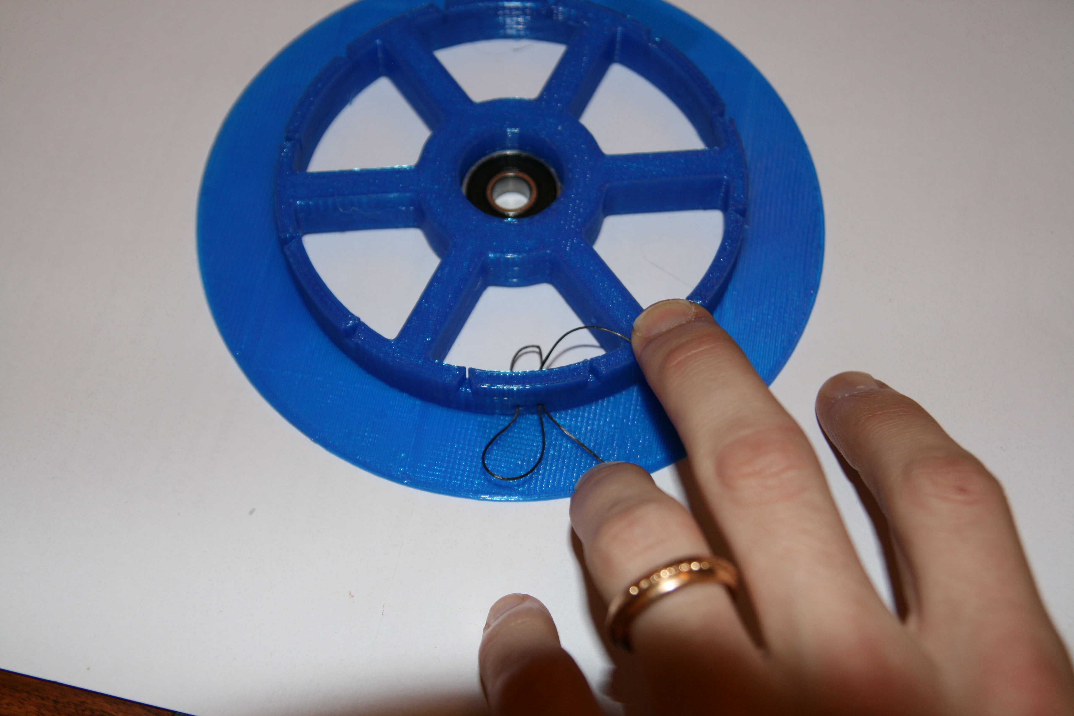
doc/v3/media/Hangprinter_Hitch_1.JPG
