blerchin/hangprinter/doc/v3/media/Hangprinter_Hitch_2.JPG

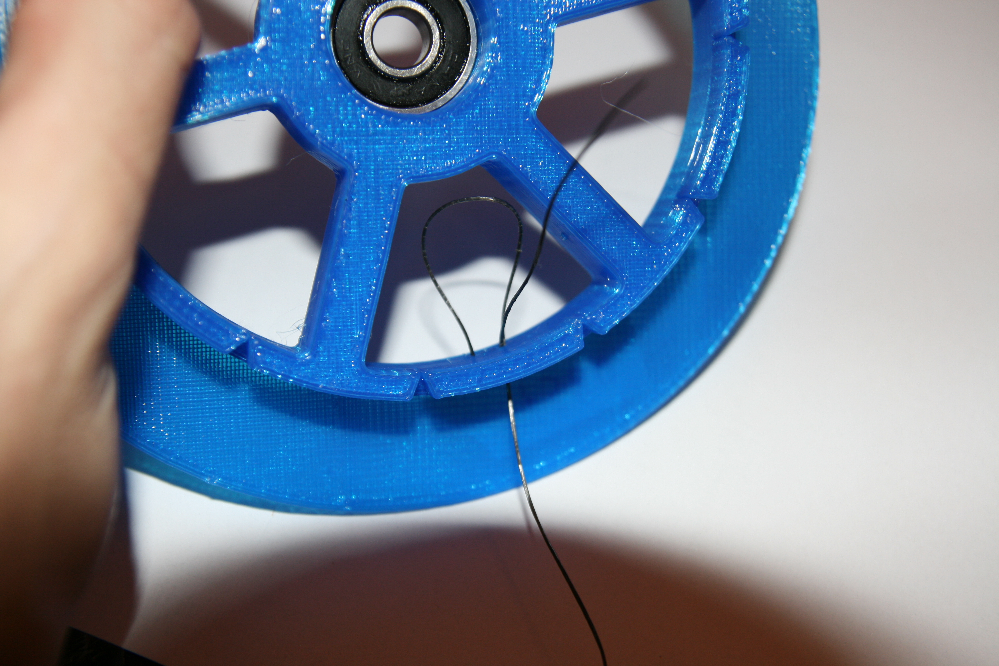
doc/v3/media/Hangprinter_Hitch_2.JPG
