blerchin/hangprinter/doc/v3/media/Hangprinter_Hitch_3.JPG

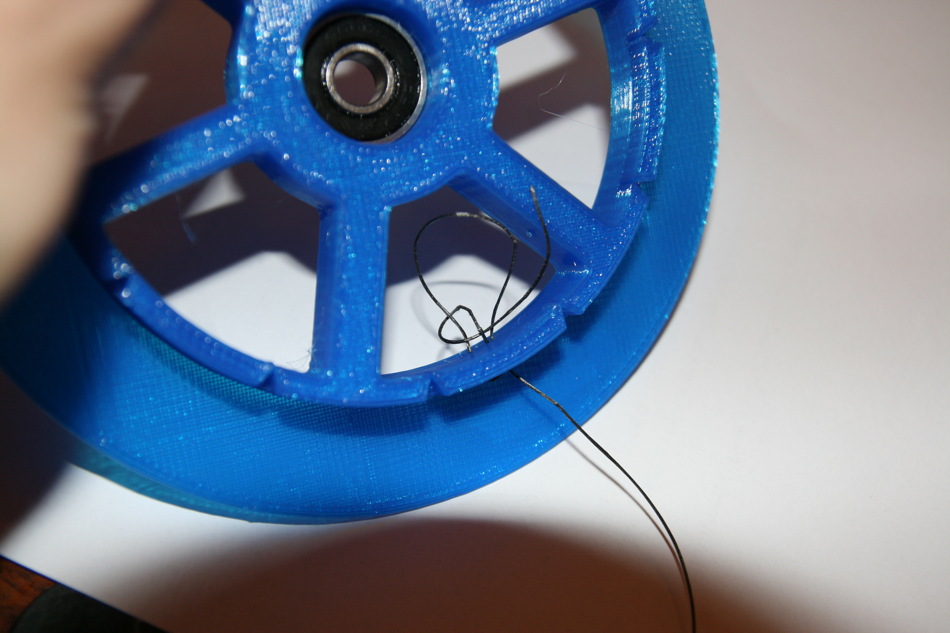
doc/v3/media/Hangprinter_Hitch_3.JPG
