blerchin/hangprinter/doc/v3/media/Hangprinter_Hitch_4.JPG

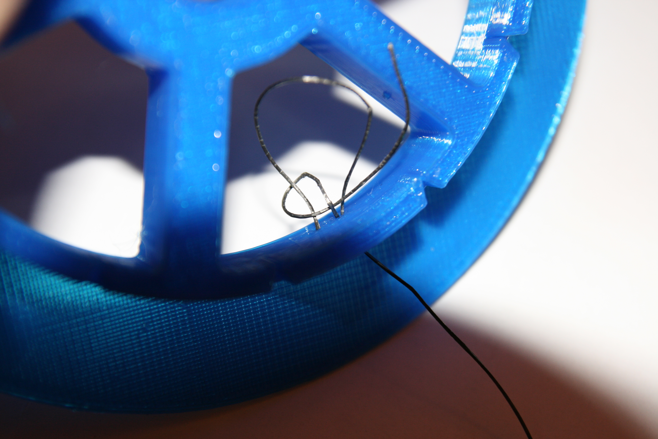
doc/v3/media/Hangprinter_Hitch_4.JPG
