blerchin/hangprinter/doc/v3/media/Hangprinter_Hitch_5.JPG

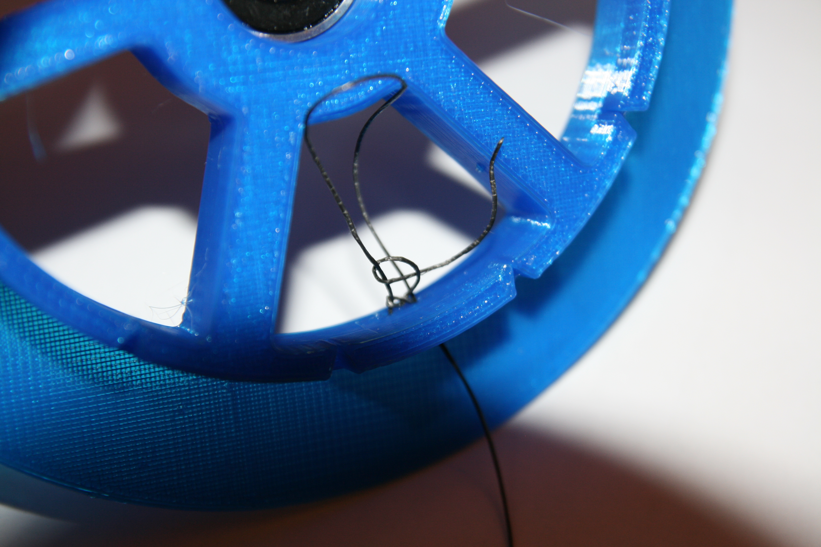
doc/v3/media/Hangprinter_Hitch_5.JPG
