blerchin/hangprinter/doc/v3/media/Hangprinter_Hitch_6.JPG

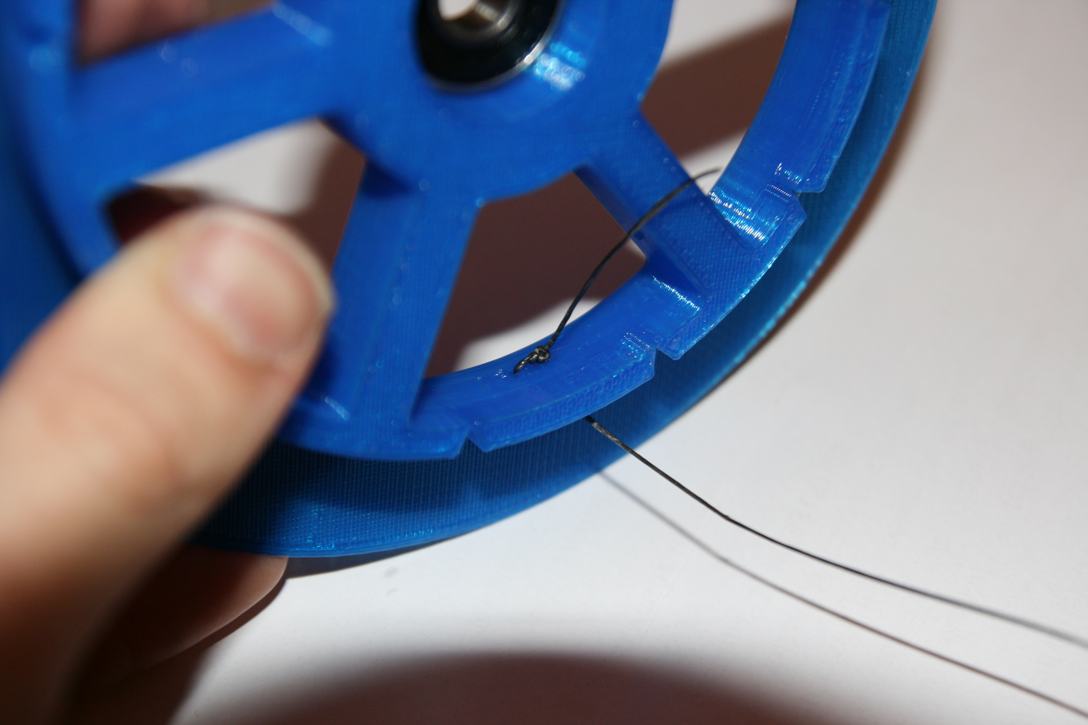
doc/v3/media/Hangprinter_Hitch_6.JPG
