blerchin/hangprinter/doc/v3/media/Hangprinter_Hitch_7.JPG

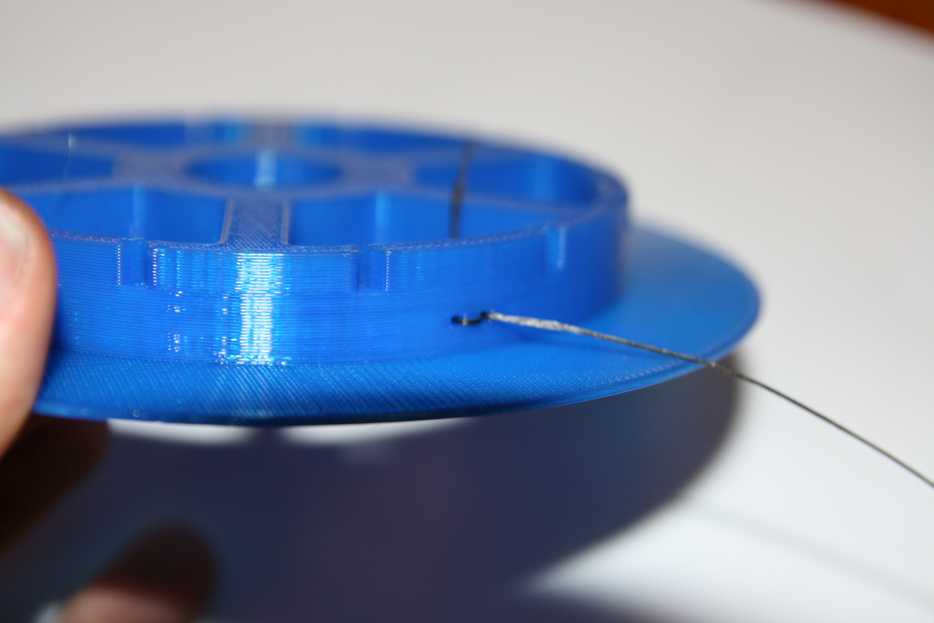
doc/v3/media/Hangprinter_Hitch_7.JPG
