blerchin/hangprinter/doc/v3/media/ziptied_crossbeam.jpg

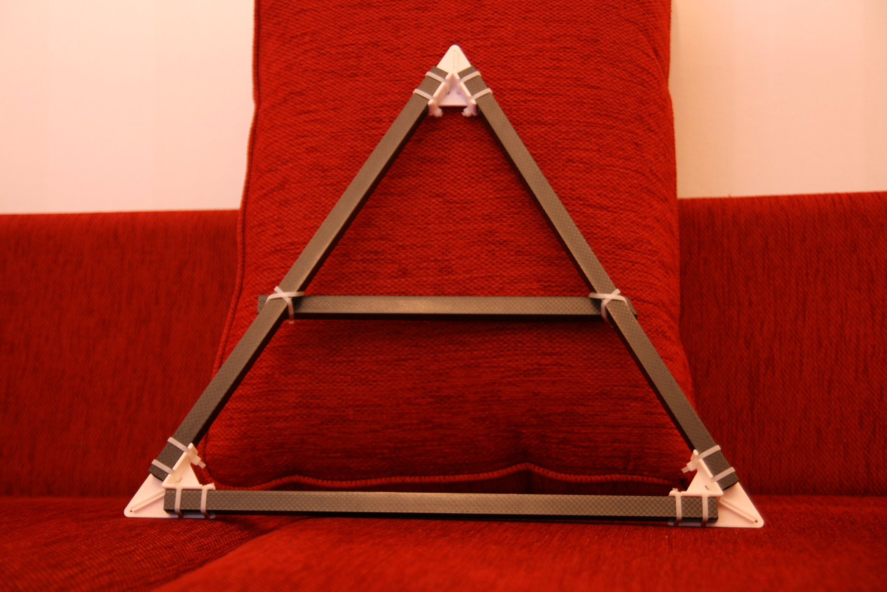
doc/v3/media/ziptied_crossbeam.jpg
