blerchin/hangprinter/openscad_stl/extruder_holder.stl

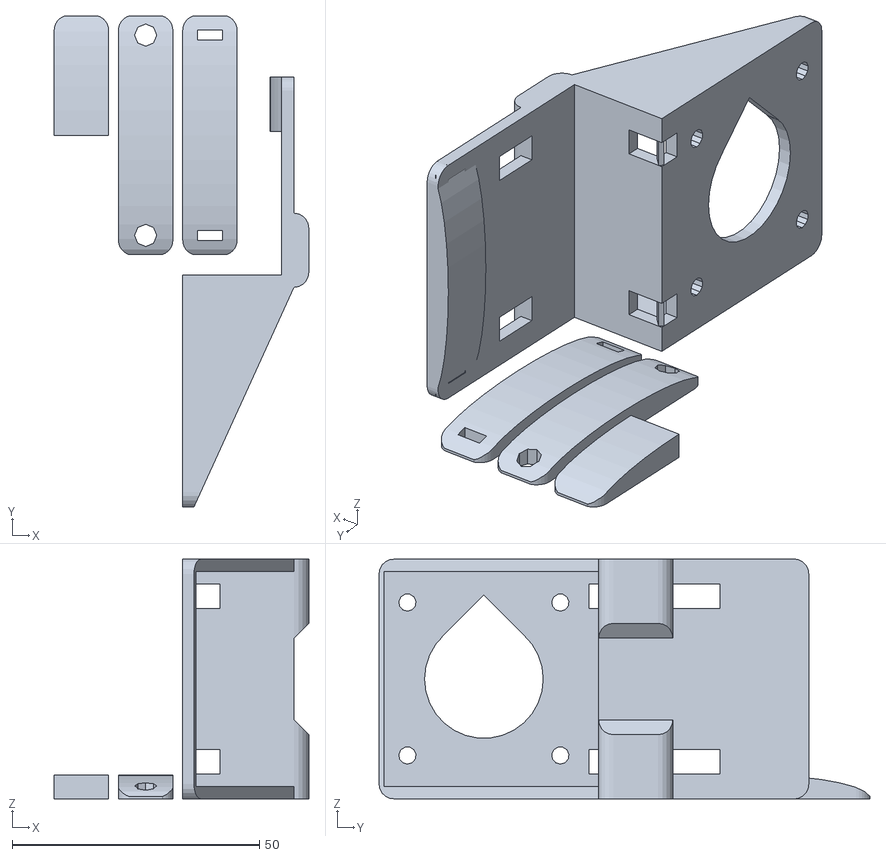
[picture p86: CAD file, 2018-11-19]
openscad_stl/extruder_holder.stl
51.5 x 99.3 x 48.5
