blerchin/hangprinter/openscad_stl/Mechaduino_standoff.stl

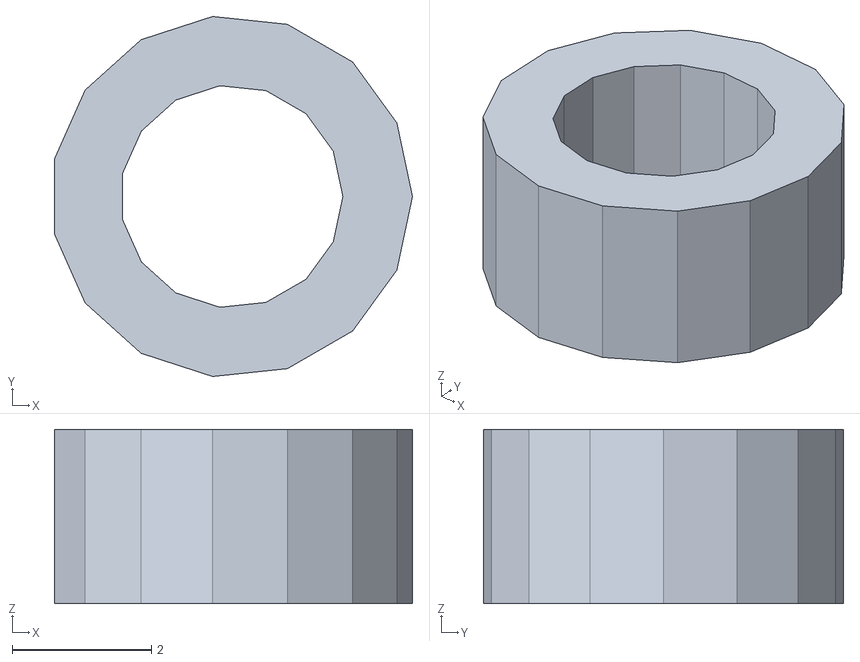
[picture p87: CAD file, 2018-11-19]
openscad_stl/Mechaduino_standoff.stl
5.14 x 5.17 x 2.50
