blerchin/hangprinter/openscad_stl/lineroller_ABC_winch.stl

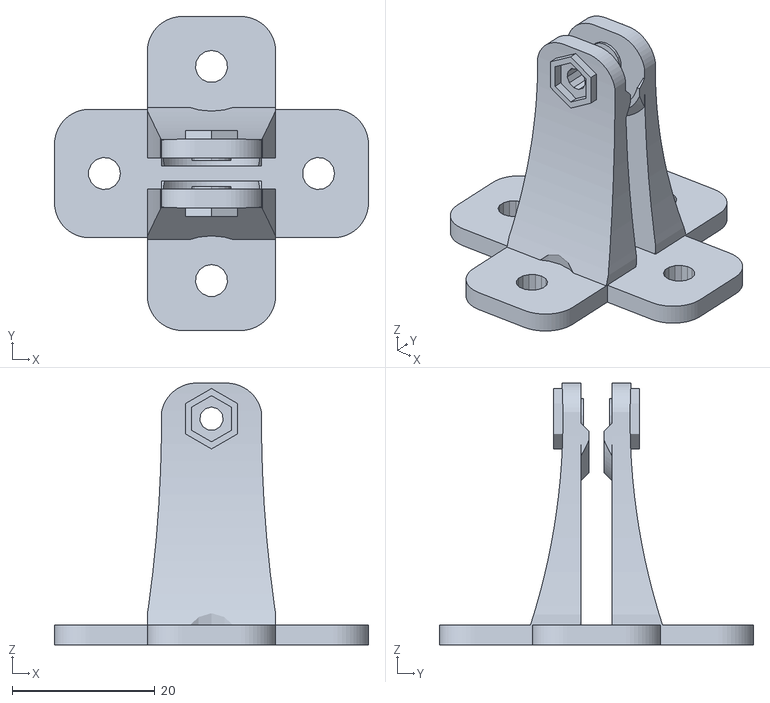
[picture p88: CAD file, 2018-11-19]
openscad_stl/lineroller_ABC_winch.stl
44.0 x 44.0 x 36.7
