blerchin/hangprinter/openscad_stl/spool.stl

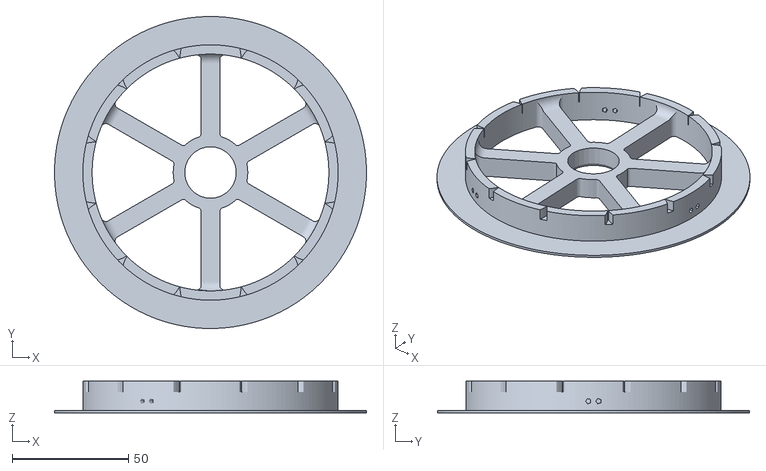
[picture p89: CAD file, 2018-11-19]
openscad_stl/spool.stl
134.4 x 134.4 x 13.6
