blerchin/hangprinter/openscad_stl/lineroller_anchor.stl

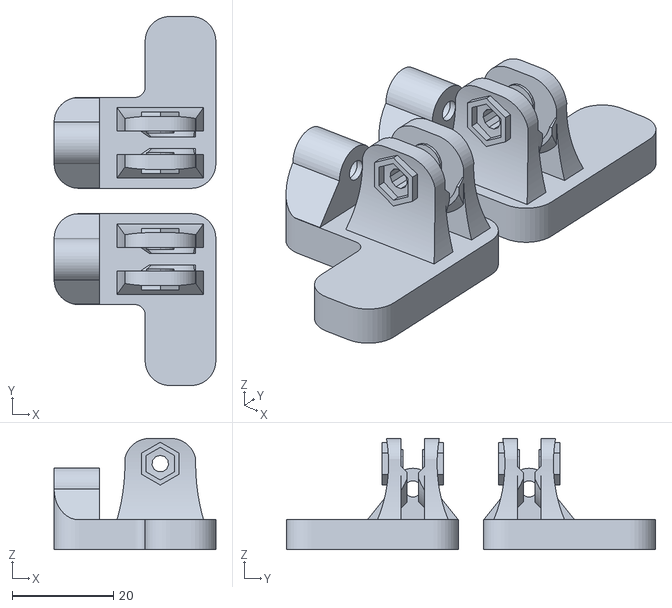
[picture p90: CAD file, 2018-11-19]
openscad_stl/lineroller_anchor.stl
32.0 x 73.0 x 22.0
