blerchin/hangprinter/openscad_stl/lineroller_anchor_template.stl

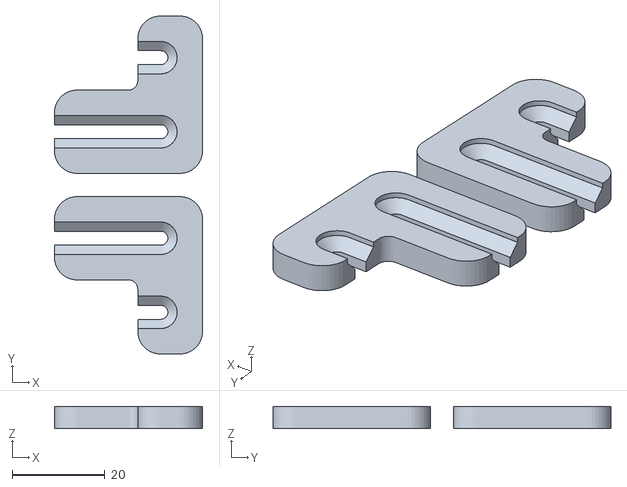
[picture p91: CAD file, 2018-11-19]
openscad_stl/lineroller_anchor_template.stl
32.0 x 73.0 x 4.80
