blerchin/hangprinter/openscad_stl/spool_gear.stl

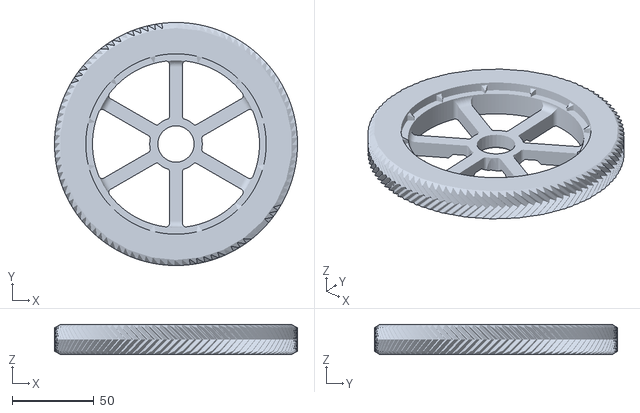
[picture p92: CAD file, 2018-11-19]
openscad_stl/spool_gear.stl
148.5 x 148.5 x 18.6
