blerchin/hangprinter/openscad_stl/lineroller_D.stl

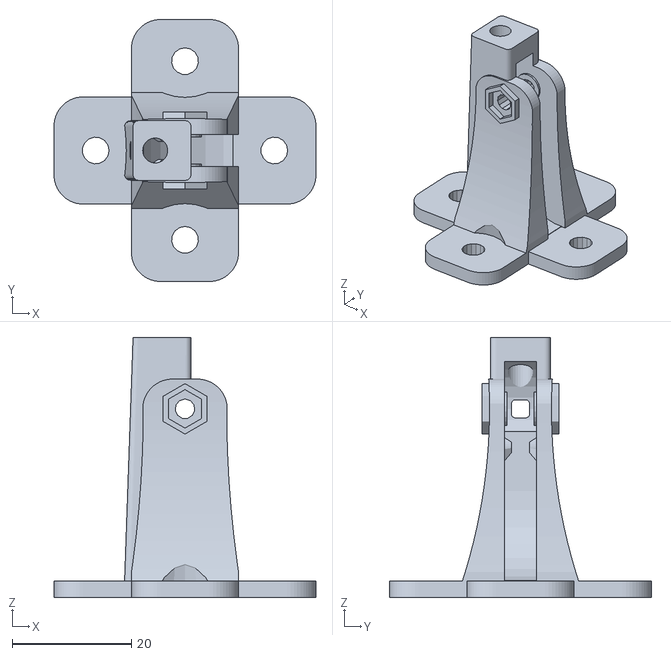
[picture p93: CAD file, 2018-11-19]
openscad_stl/lineroller_D.stl
44.0 x 44.0 x 43.7
