blerchin/hangprinter/openscad_stl/spacer.stl

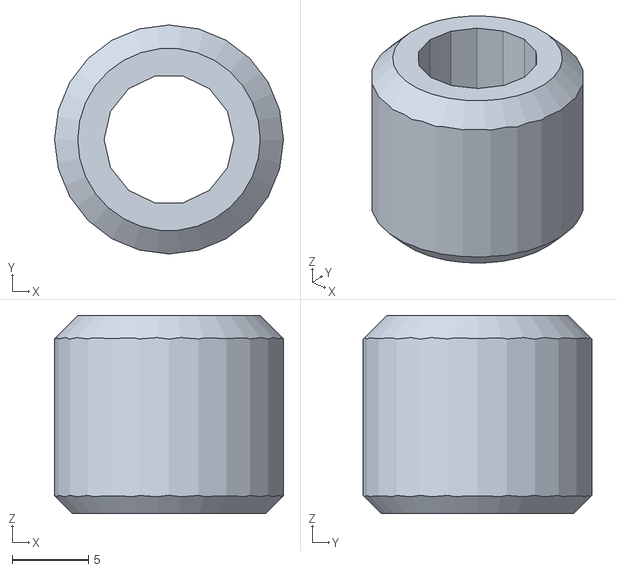
[picture p94: CAD file, 2018-11-19]
openscad_stl/spacer.stl
15.0 x 15.0 x 13.0
