blerchin/hangprinter/openscad_stl/corner_clamp.stl

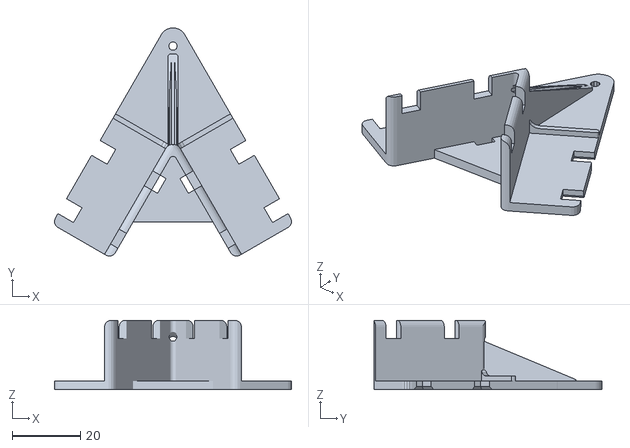
[picture p95: CAD file, 2018-11-19]
openscad_stl/corner_clamp.stl
69.2 x 66.6 x 20.2
