blerchin/hangprinter/openscad_stl/spool_core.stl

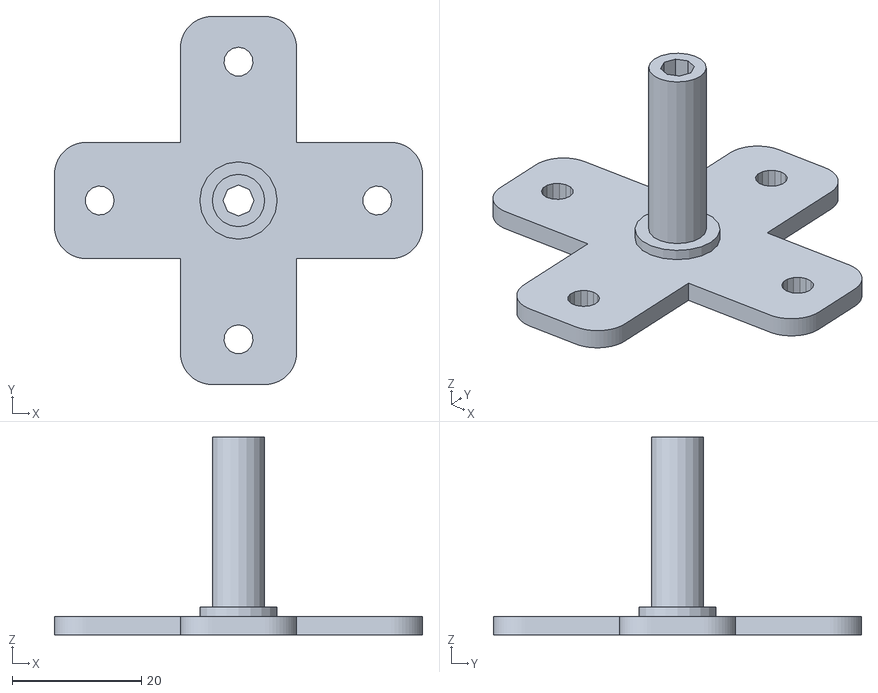
[picture p96: CAD file, 2018-11-19]
openscad_stl/spool_core.stl
57.0 x 57.0 x 30.6
