blerchin/hangprinter/openscad_stl/cable_clamp.stl

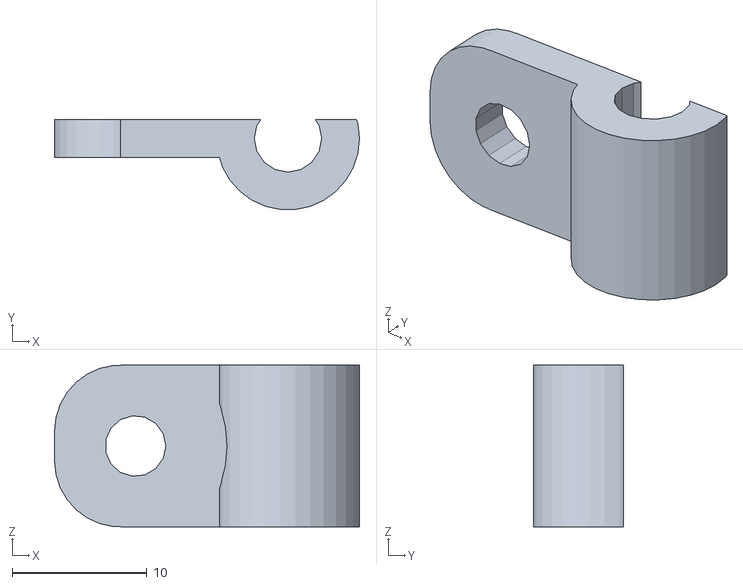
[picture p97: CAD file, 2018-11-19]
openscad_stl/cable_clamp.stl
22.6 x 6.67 x 12.0
