blerchin/hangprinter/doc/v3/media/Mechaduino_assembly/000.JPG

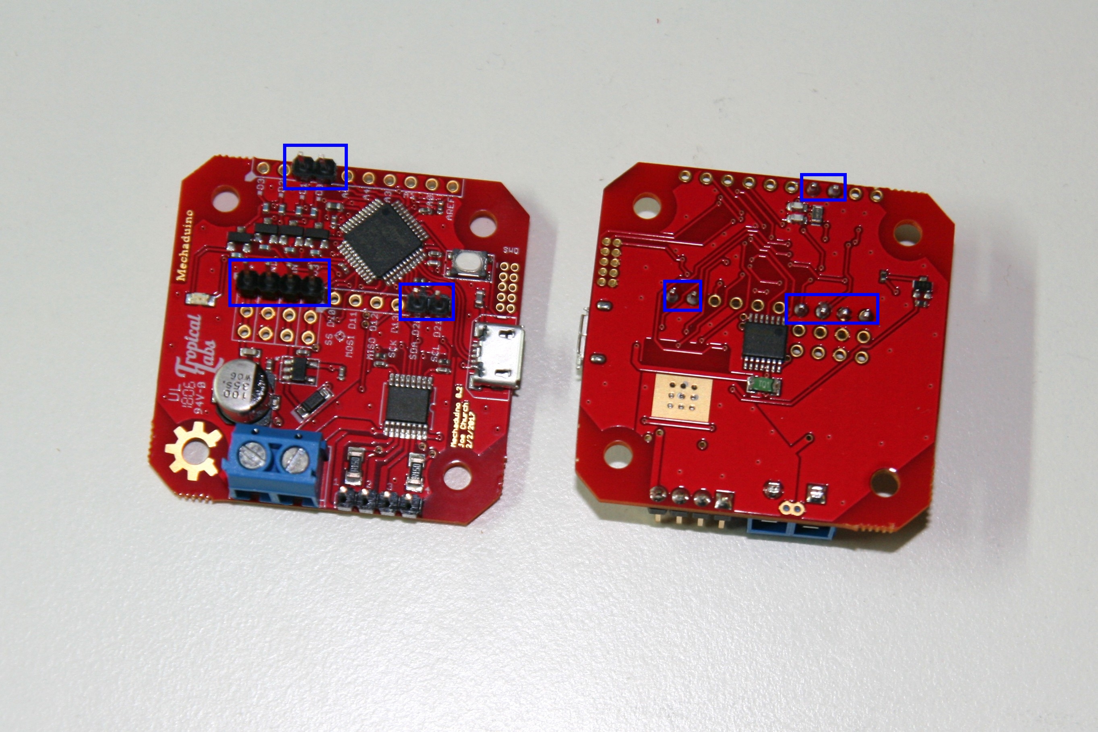
doc/v3/media/Mechaduino_assembly/000.JPG
