blerchin/hangprinter/doc/v3/media/Mechaduino_assembly/001.JPG

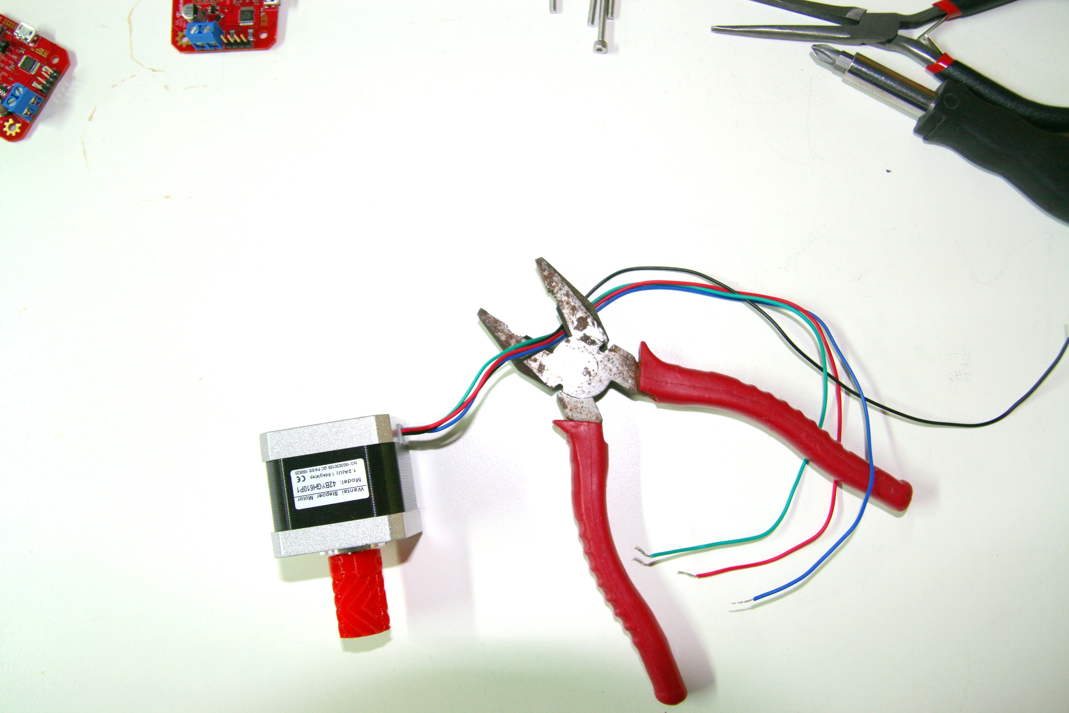
doc/v3/media/Mechaduino_assembly/001.JPG
