blerchin/hangprinter/doc/v3/media/Mechaduino_assembly/003.JPG

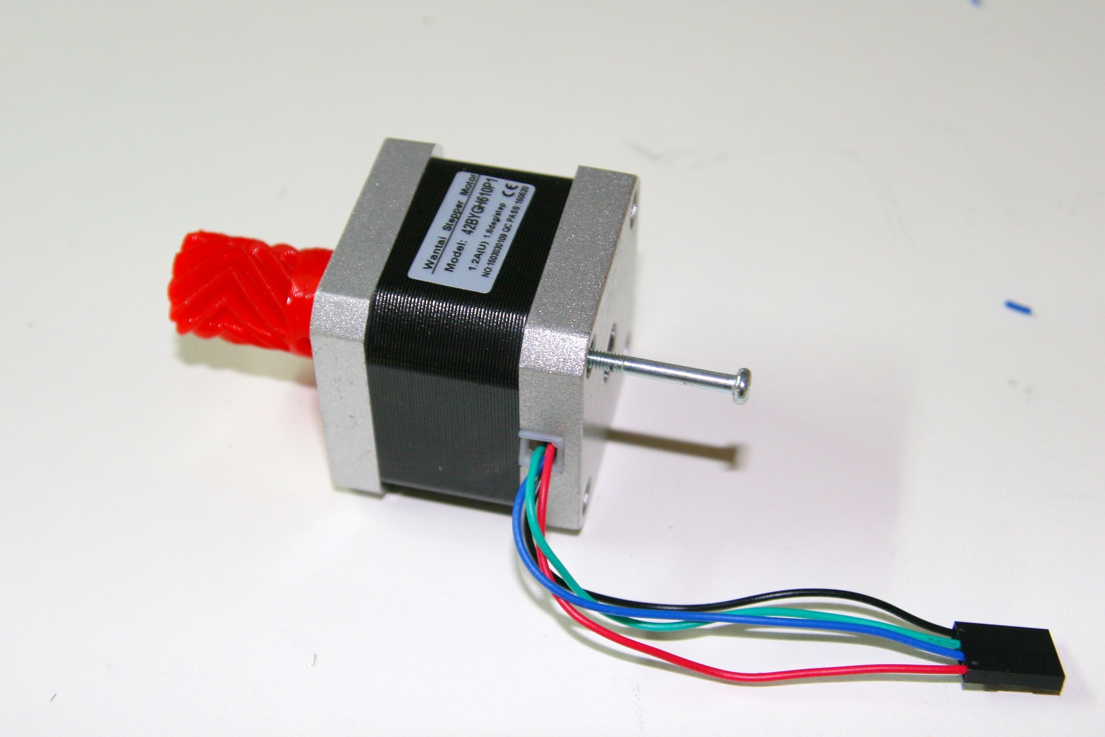
doc/v3/media/Mechaduino_assembly/003.JPG
