blerchin/hangprinter/doc/v3/media/Mechaduino_assembly/004.JPG

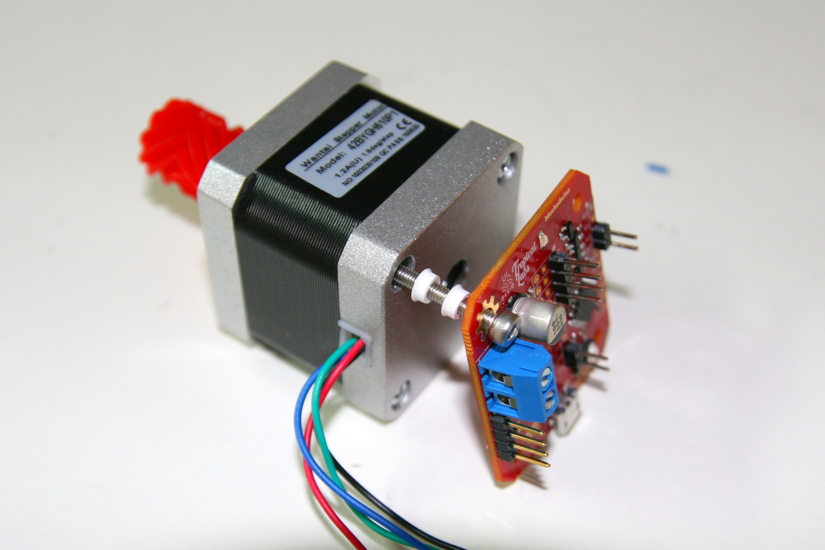
doc/v3/media/Mechaduino_assembly/004.JPG
