blerchin/hangprinter/doc/v3/media/Mechaduino_assembly/006.JPG

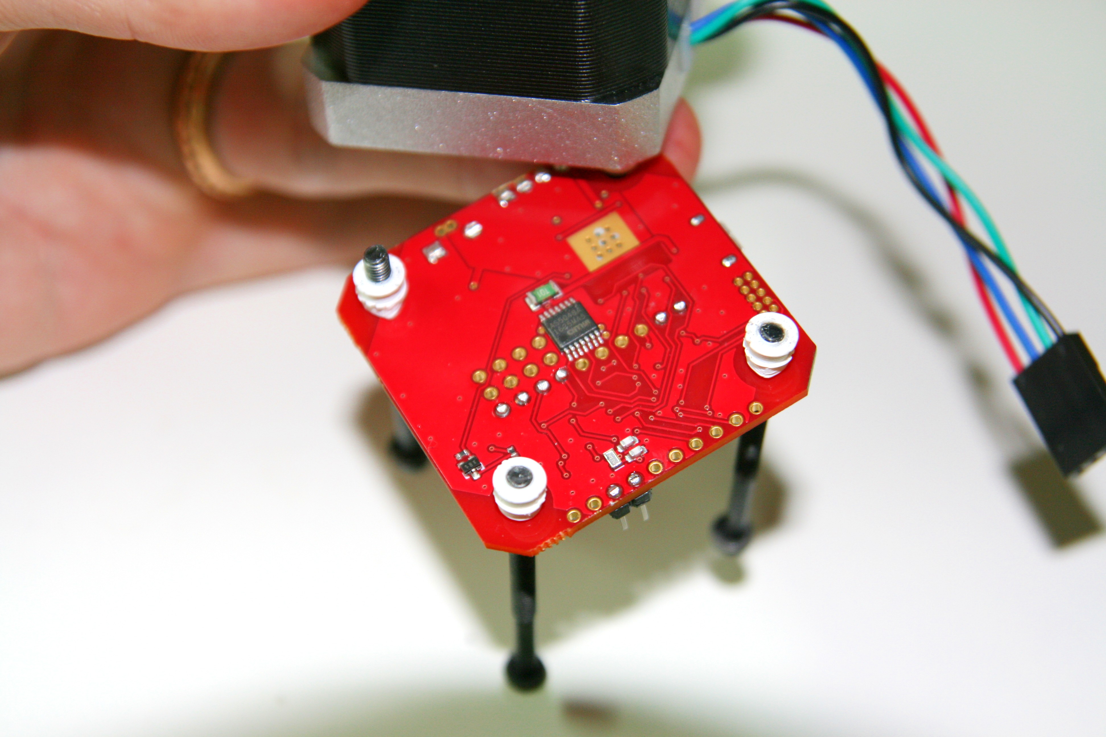
doc/v3/media/Mechaduino_assembly/006.JPG
