blerchin/hangprinter/doc/v3/media/Mechaduino_assembly/007.JPG

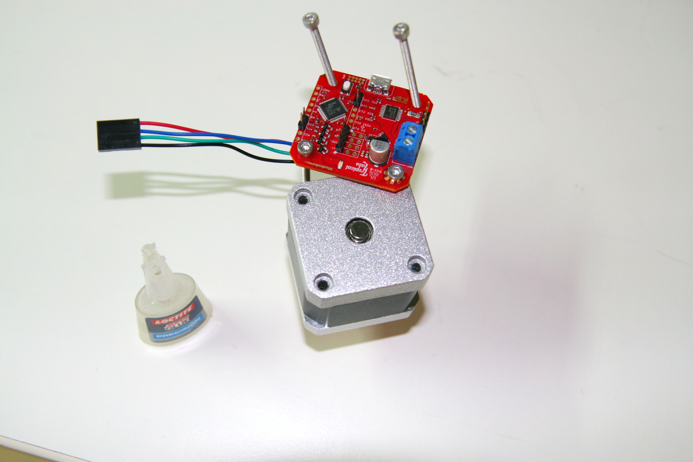
doc/v3/media/Mechaduino_assembly/007.JPG
