blerchin/hangprinter/doc/v3/media/Mechaduino_assembly/008.JPG

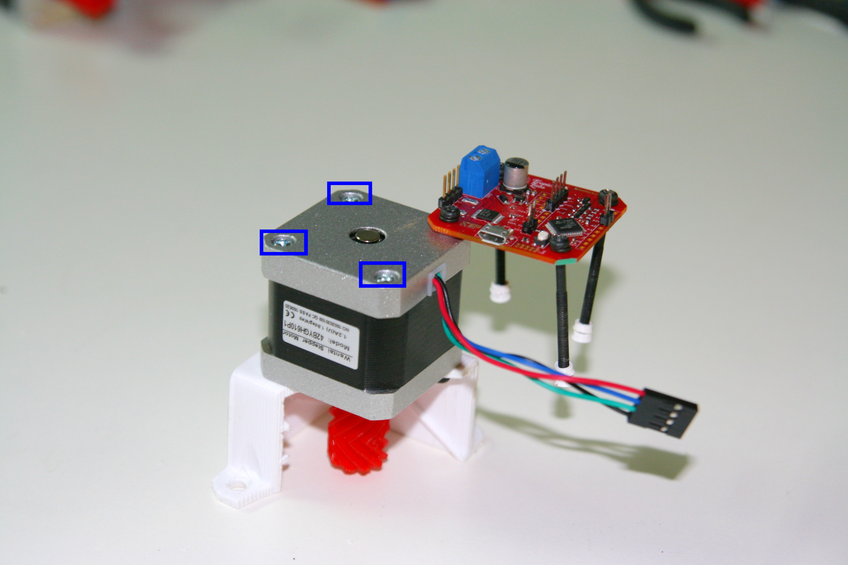
doc/v3/media/Mechaduino_assembly/008.JPG
