blerchin/hangprinter/doc/v3/media/Mechaduino_assembly/009.JPG

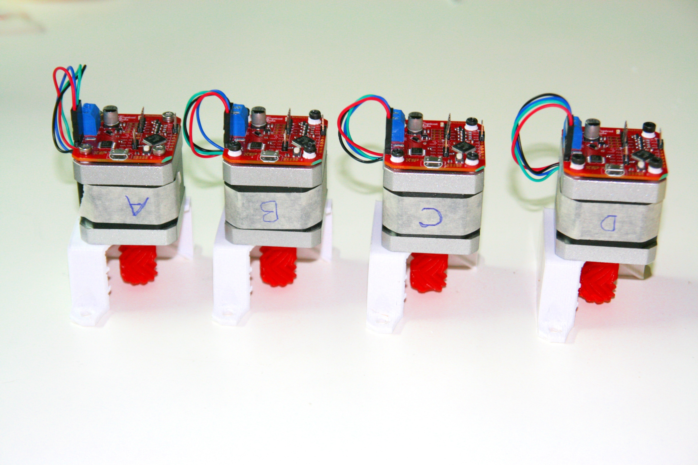
doc/v3/media/Mechaduino_assembly/009.JPG
