blerchin/hangprinter/doc/v3/media/Mechaduino_assembly/010.JPG

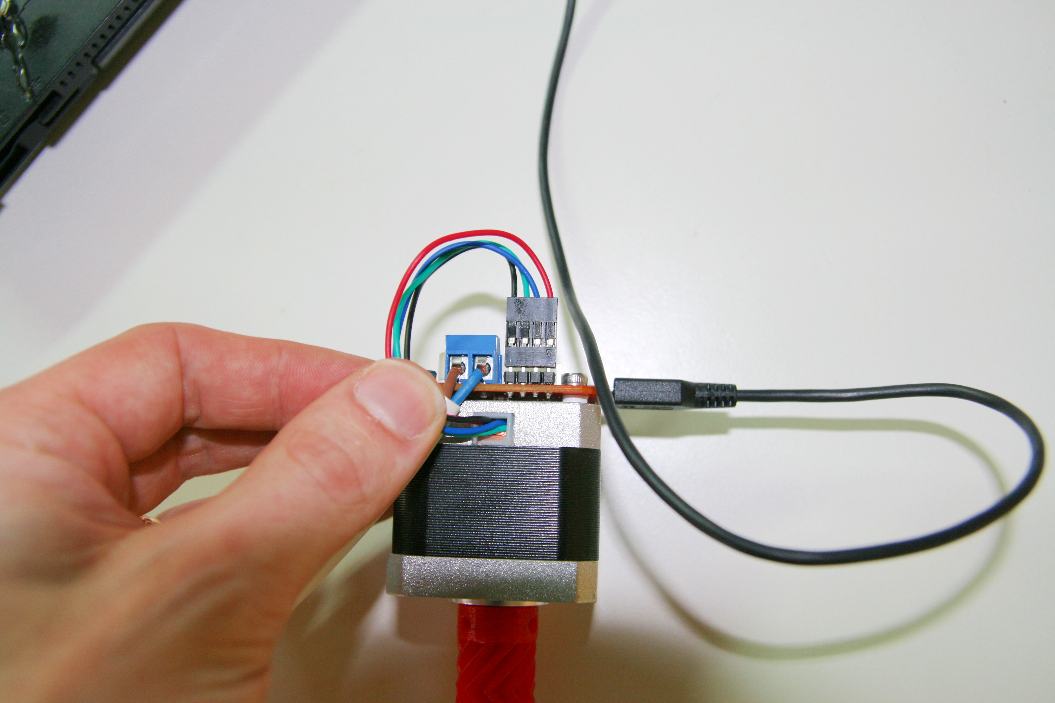
doc/v3/media/Mechaduino_assembly/010.JPG
