blerchin/hangprinter/doc/v3/media/Mechaduino_assembly/lookup.png

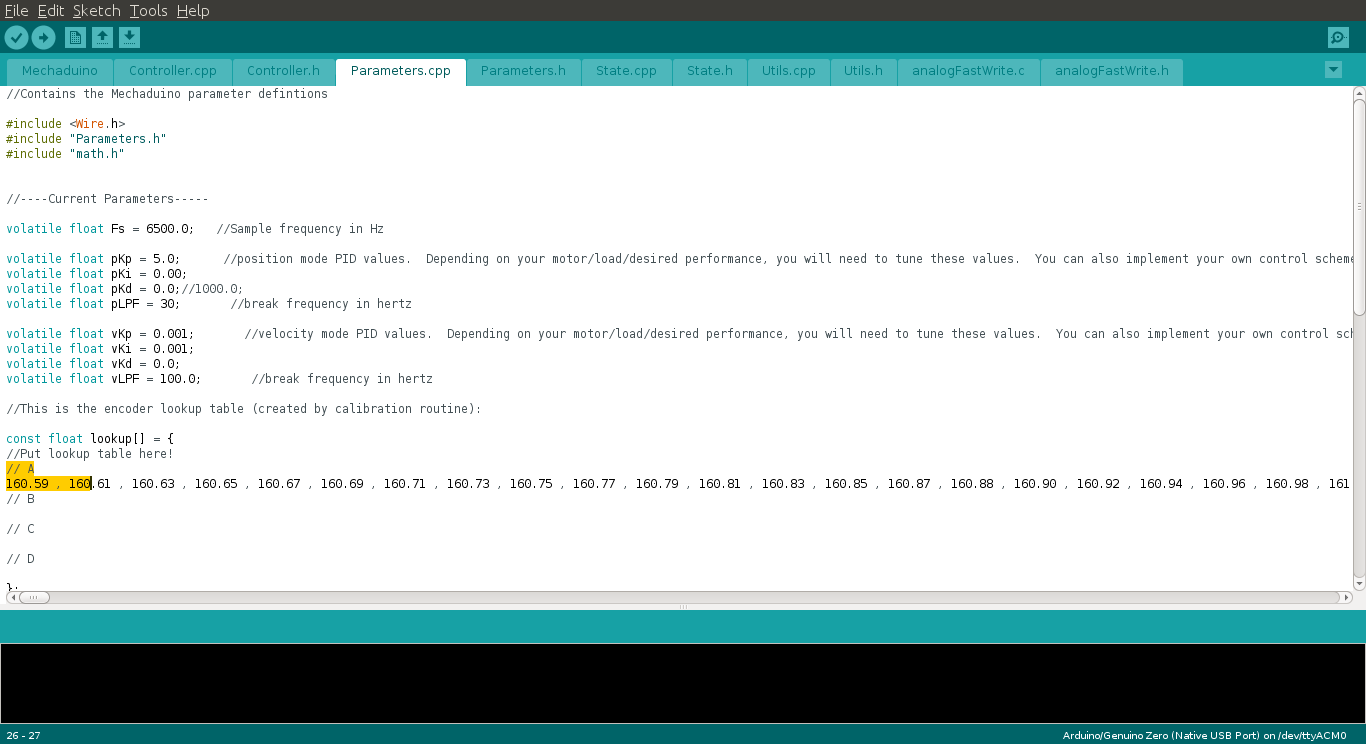
doc/v3/media/Mechaduino_assembly/lookup.png
