blerchin/hangprinter/doc/v3/media/Mechaduino_assembly/parameters_dot_h_i2c_addr.png

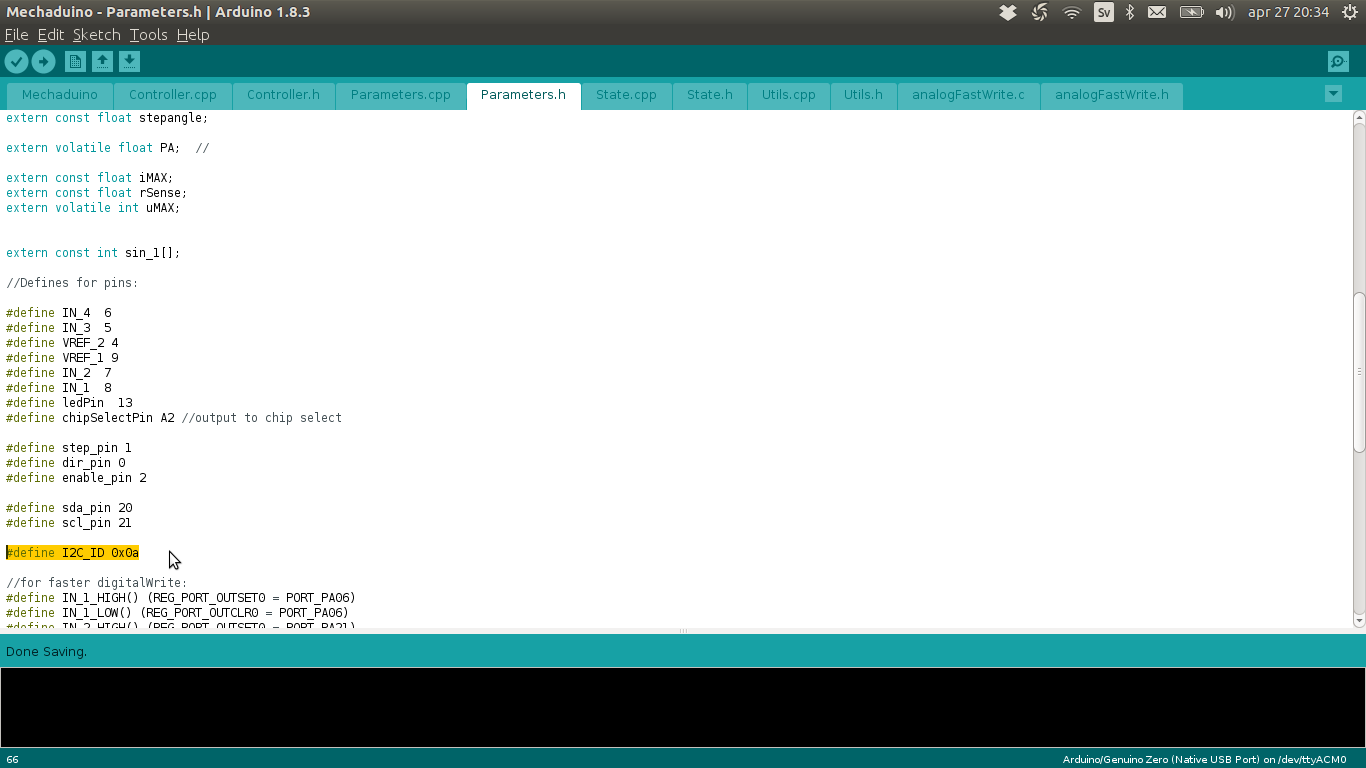
doc/v3/media/Mechaduino_assembly/parameters_dot_h_i2c_addr.png
