blerchin/hangprinter/doc/v3/media/Mechaduino_assembly/PID.png

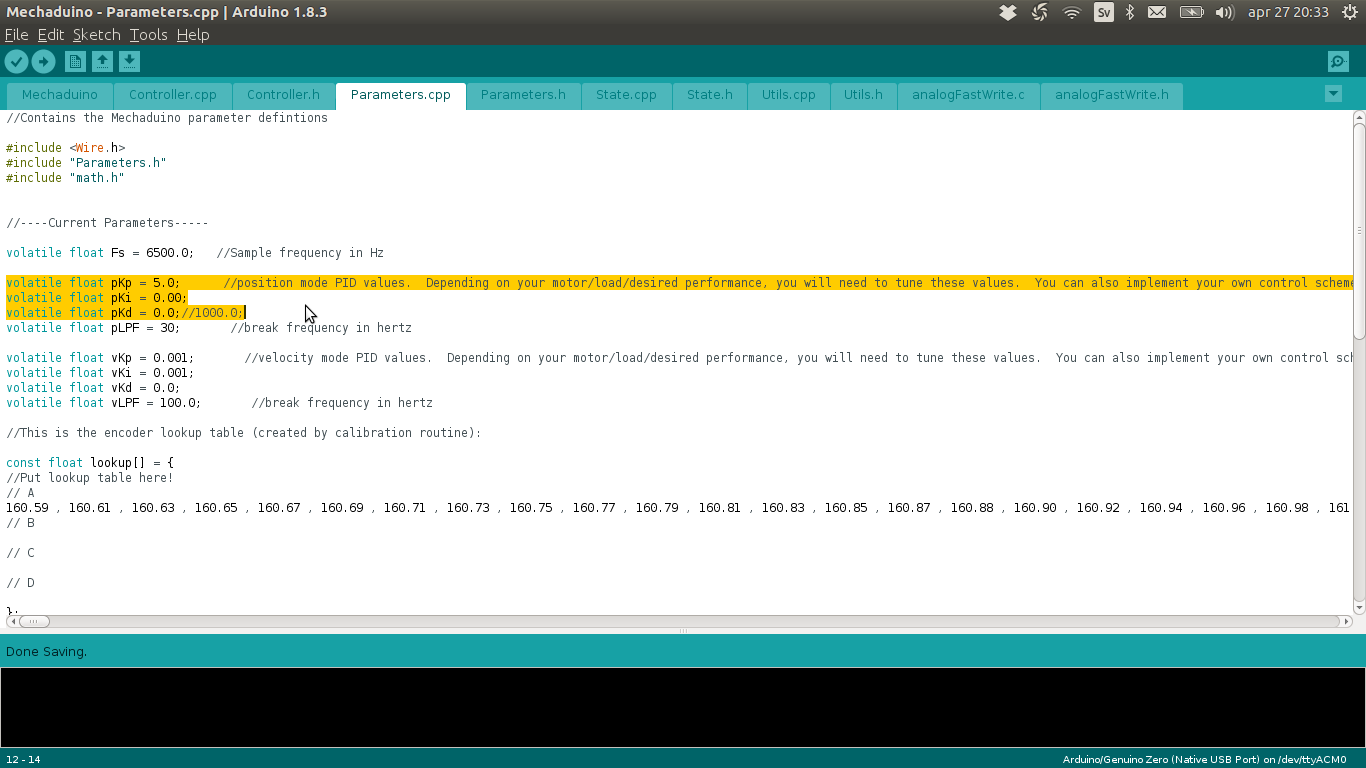
doc/v3/media/Mechaduino_assembly/PID.png
