blerchin/hangprinter/doc/v3/media/Mechaduino_assembly/serial_monitor_usage.png

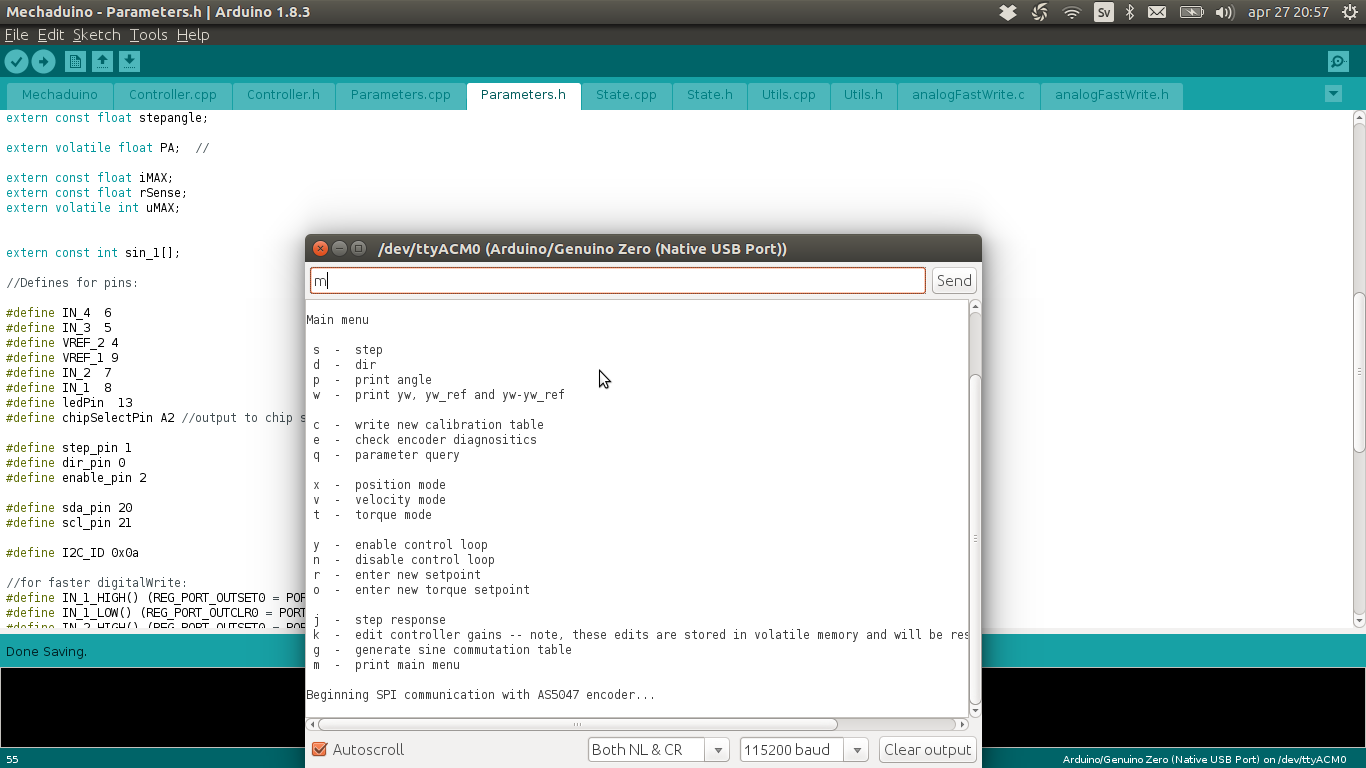
doc/v3/media/Mechaduino_assembly/serial_monitor_usage.png
