blerchin/hangprinter/doc/v3/media/Mechaduino_assembly/small_tools_menu2.png

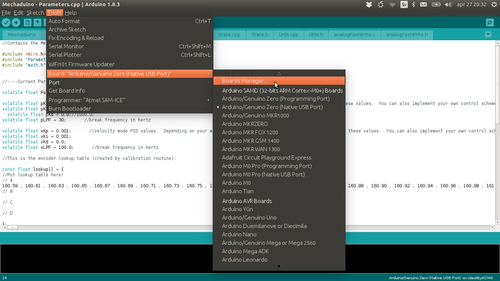
doc/v3/media/Mechaduino_assembly/small_tools_menu2.png
