blerchin/hangprinter/doc/v3/media/Mechaduino_assembly/small_upload_mechaduino_firmware.JPG

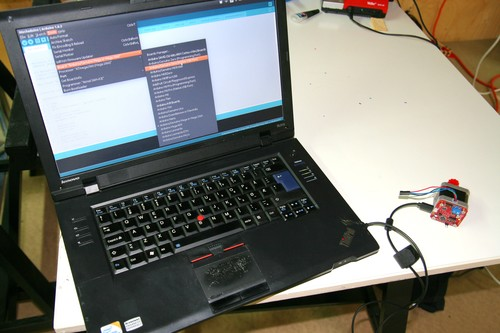
doc/v3/media/Mechaduino_assembly/small_upload_mechaduino_firmware.JPG
