blerchin/hangprinter/doc/v3/media/Mechaduino_assembly/small_verbose_upload_e.png

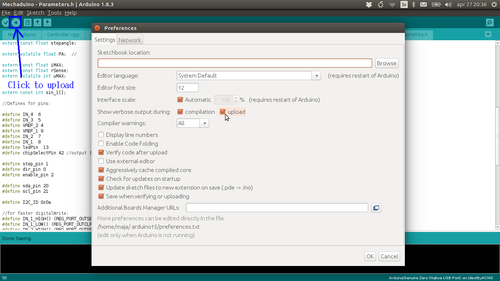
doc/v3/media/Mechaduino_assembly/small_verbose_upload_e.png
