blerchin/hangprinter/doc/v3/media/Mechaduino_assembly/small_zeroboard.png

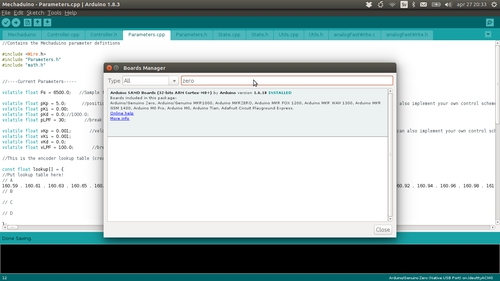
doc/v3/media/Mechaduino_assembly/small_zeroboard.png
