blerchin/hangprinter/doc/v3/media/print_template_to_scale.JPG

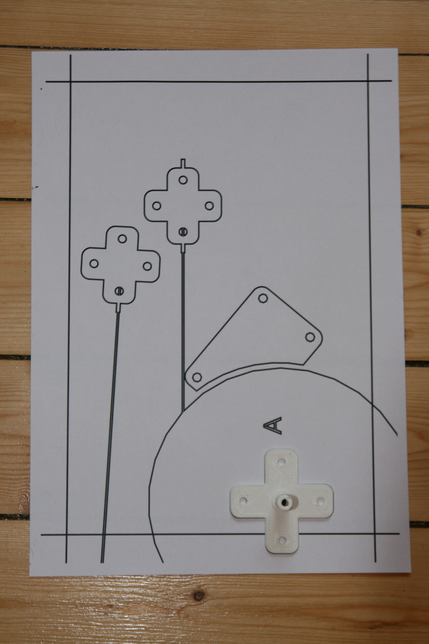
doc/v3/media/print_template_to_scale.JPG
