blerchin/hangprinter/firmware/SmartStepper_subtree/firmware/stepper_nano_zero/sine.cpp

/*
 * since.cpp
 *
 *  Created on: Dec 24, 2016
 *      Author: tstern
 *
 *	Misfit Tech invests time and resources providing this open source code,
 *	please support Misfit Tech and open-source hardware by purchasing
 *	products from Misfit Tech, www.misifittech.net!
 *
 *	Written by Trampas Stern  for Misfit Tech.
 *	BSD license, check license.txt for more information
 *	All text above, must be included in any redistribution
 *********************************************************************/

#include "sine.h"

#pragma GCC push_options
#pragma GCC optimize ("-Ofast")

#ifdef NZS_FAST_SINE
static const int16_t sineTable[1280]={
0,201,402,603,804,1005,1206,1407,1608,1808,2009,2210,2410,2611,2811,3011,
3212,3412,3611,3811,4011,4210,4410,4609,4808,5007,5205,5404,5602,5800,5998,6195,
6392,6589,6786,6983,7179,7375,7571,7766,7962,8156,8351,8545,8739,8933,9126,9319,
9512,9704,9896,10087,10278,10469,10659,10849,11039,11228,11417,11605,11793,11980,12167,12353,
12539,12725,12910,13094,13278,13462,13645,13828,14010,14191,14372,14553,14732,14912,15090,15269,
15446,15623,15800,15976,16151,16325,16499,16673,16846,17018,17189,17360,17530,17700,17869,18037,
18204,18371,18537,18703,18868,19032,19195,19357,19519,19680,19841,20000,20159,20317,20475,20631,
20787,20942,21097,21250,21403,21554,21705,21856,22005,22154,22301,22448,22594,22739,22884,23027,
23170,23312,23452,23592,23732,23870,24007,24143,24279,24413,24547,24680,24812,24942,25072,25201,
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
		57797,57985,58171,58356,58537,58717,58895,59070,59243,59414,59582,59749,59913,60075,60234,60391,
		60546,60699,60850,60998,61144,61287,61429,61567,61704,61838,61970,62100,62227,62352,62475,62595,
		62713,62829,62942,63053,63161,63267,63371,63472,63571,63668,63762,63853,63943,64030,64114,64196,
		64276,64353,64428,64500,64570,64638,64703,64765,64826,64883,64939,64992,65042,65090,65136,65179,
		65219,65258,65293,65327,65357,65386,65412,65435,65456,65475,65491,65504,65515,65524,65530,65534,
		65535,
};
#endif




int16_t sine(uint16_t angle)
{
#ifdef NZS_FAST_SINE
	return sineTable[angle];
#else
	int sign=1;
	int16_t ret;
	//our sine table has 1024 points per rotation so convert angle to closest step

	if (angle>=(SINE_STEPS/2))
	{
		sign=-1;
	}

	angle=angle % (SINE_STEPS/2); //limit to 0-180 as sign takes care of 180-360

	if (angle>(SINE_STEPS/4-1))  //if we are greater than 90 we need to look up table backwards
	{
		angle=(SINE_STEPS/2)-angle;
	}

	ret=(int16_t)(sineTable[angle]/2)*sign;
	return ret;
#endif
}

int16_t cosine(uint16_t angle)
{
#ifdef NZS_FAST_SINE
	angle=angle+(SINE_STEPS/4);
	return sineTable[angle];
#else

	int sign=1;
	int16_t ret;
	//our sine table has 1024 points per rotation so convert angle to closest step

	if (angle>=(SINE_STEPS/4) and angle<(3*(SINE_STEPS/4)))
	{
		sign=-1;
	}

	angle=angle % (SINE_STEPS/2); //limit to 0-180 as sign takes care of 180-360

	if (angle>(SINE_STEPS/4-1))  //if we are greater than 90 we need to look up table backwards
	{
		angle=(SINE_STEPS/2)-angle;
	}

	//for cosine we need 90 degree phase shift
	angle=(SINE_STEPS/4)-angle;

	ret=(int16_t)(sineTable[angle]/2)*sign;
	return ret;
#endif
}

#pragma GCC pop_options
