blerchin/hangprinter/firmware/SmartStepper_subtree/firmware/stepper_nano_zero/ftoa.h

/*
 * ftoa.h
 *
 *  Created on: Jan 6, 2017
 *      Author: tstern
 */

#ifndef FTOA_H_
#define FTOA_H_

#define MAX_MANTISA (1000)

int ftoa (float x, char *str, char  prec, char format);



#endif /* FTOA_H_ */
